ESPWortuhr/Multilayout-ESP-Wordclock/pics/CNC_Machined/uhr242_beschriftung.jpg

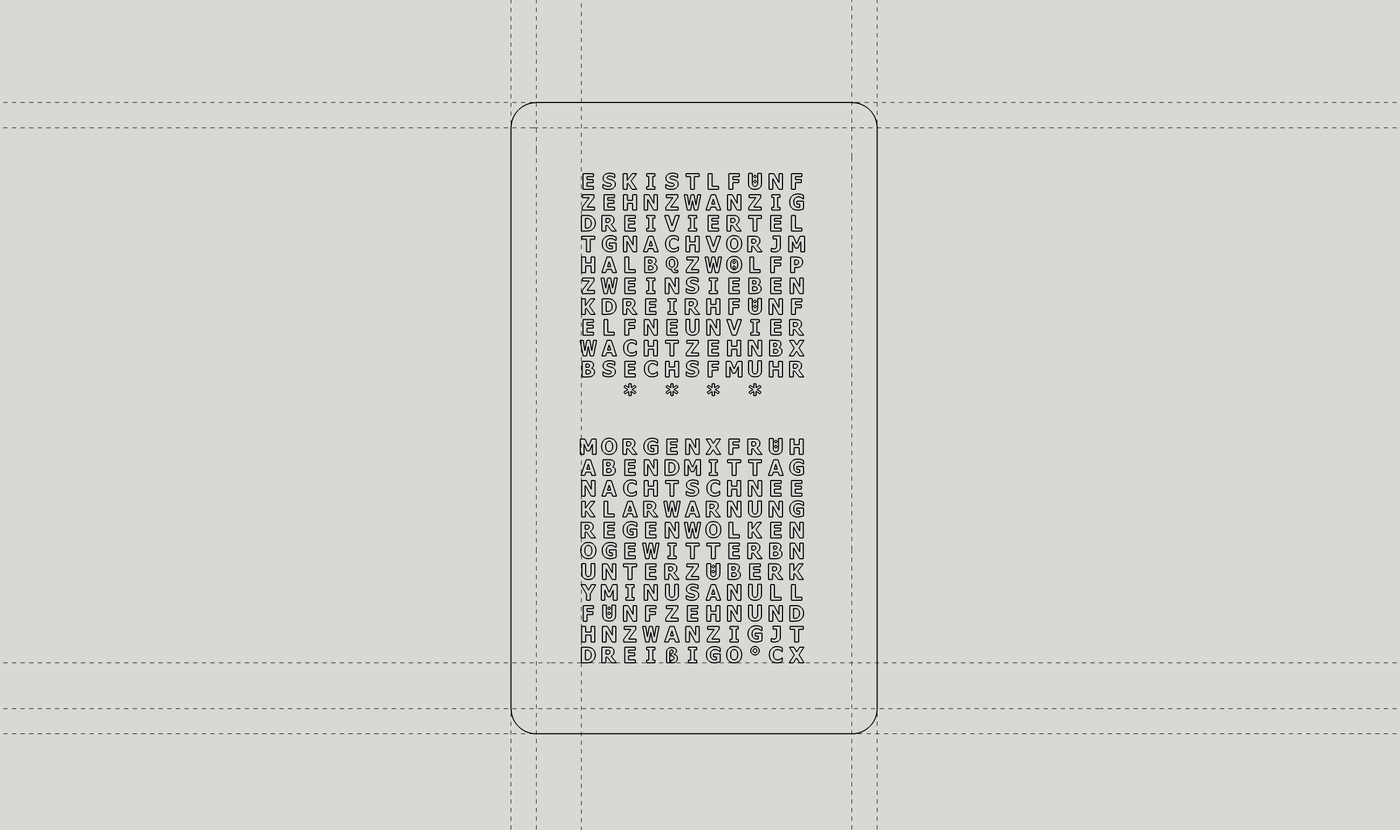
pics/CNC_Machined/uhr242_beschriftung.jpg
