ESPWortuhr/Multilayout-ESP-Wordclock/pics/CNC_Machined/uhr_242-back.jpg

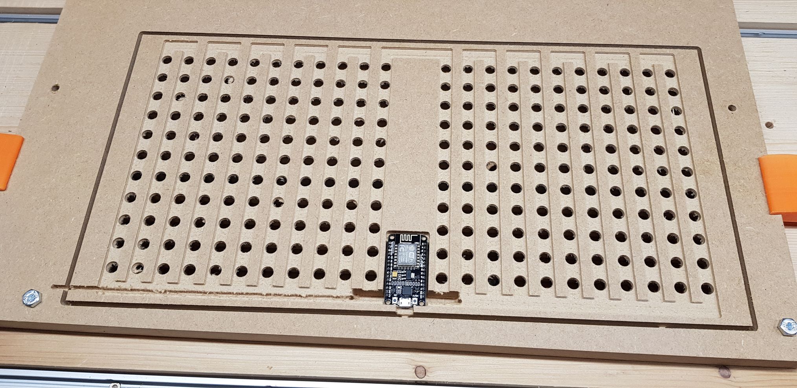
pics/CNC_Machined/uhr_242-back.jpg
