ESPWortuhr/Multilayout-ESP-Wordclock/pics/uhr.jpg

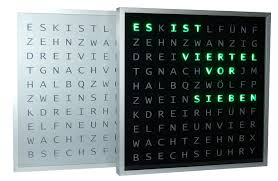
pics/uhr.jpg
