ESPWortuhr/Multilayout-ESP-Wordclock/pics/Lasercutted/UHR114_Step_1.jpg

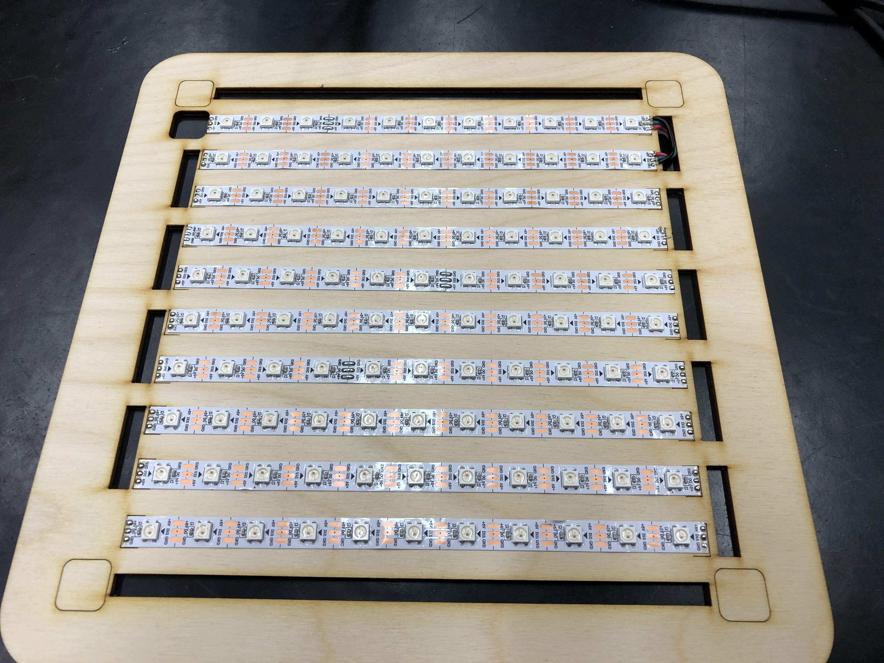
pics/Lasercutted/UHR114_Step_1.jpg
