ESPWortuhr/Multilayout-ESP-Wordclock/pics/Lasercutted/UHR114_Step_2.jpg

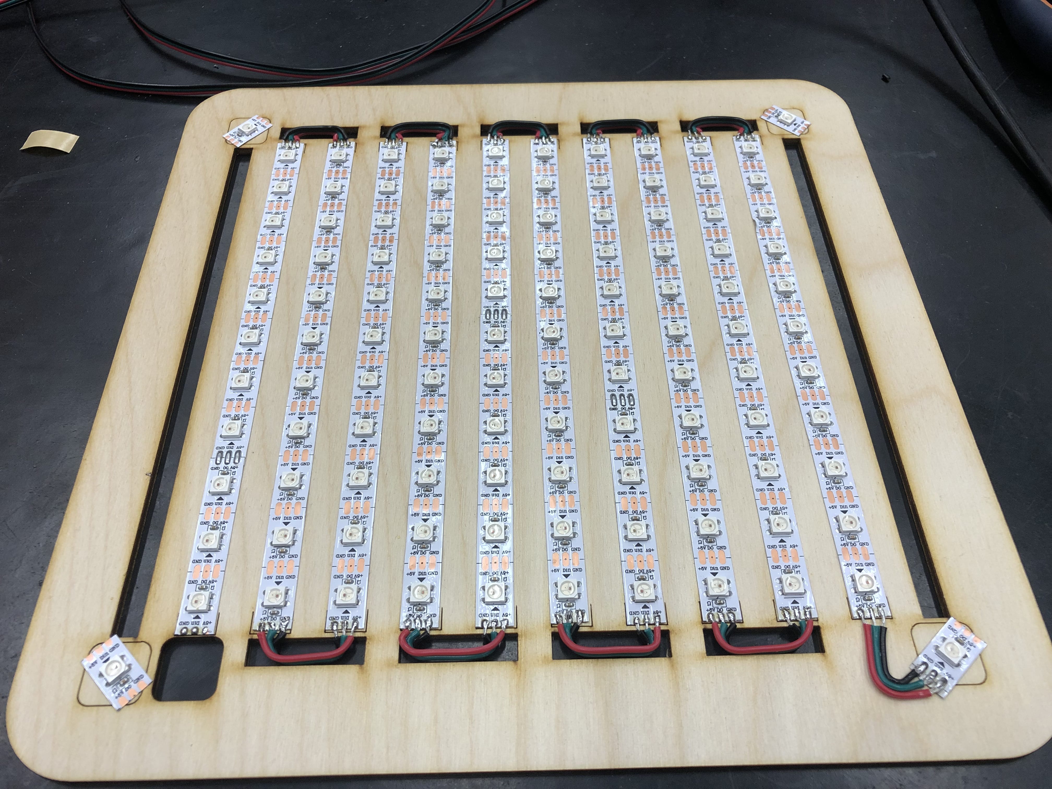
pics/Lasercutted/UHR114_Step_2.jpg
