ESPWortuhr/Multilayout-ESP-Wordclock/pics/Lasercutted/UHR114_Step_3.jpg

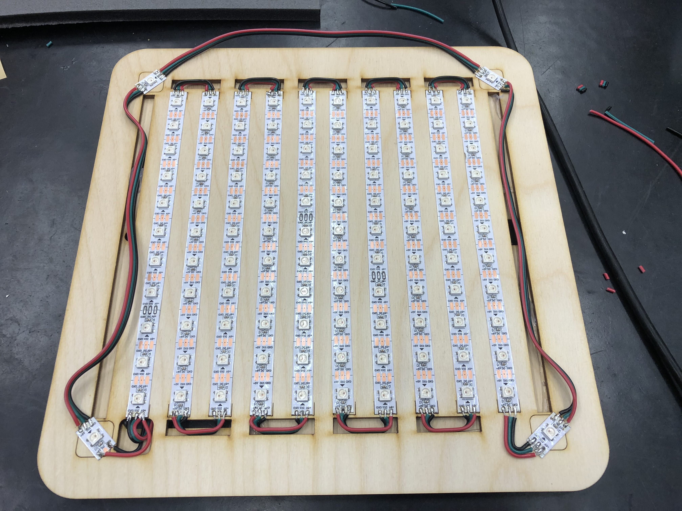
pics/Lasercutted/UHR114_Step_3.jpg
