ESPWortuhr/Multilayout-ESP-Wordclock/pics/Lasercutted/UHR114_Step_Front_Assembly.jpg

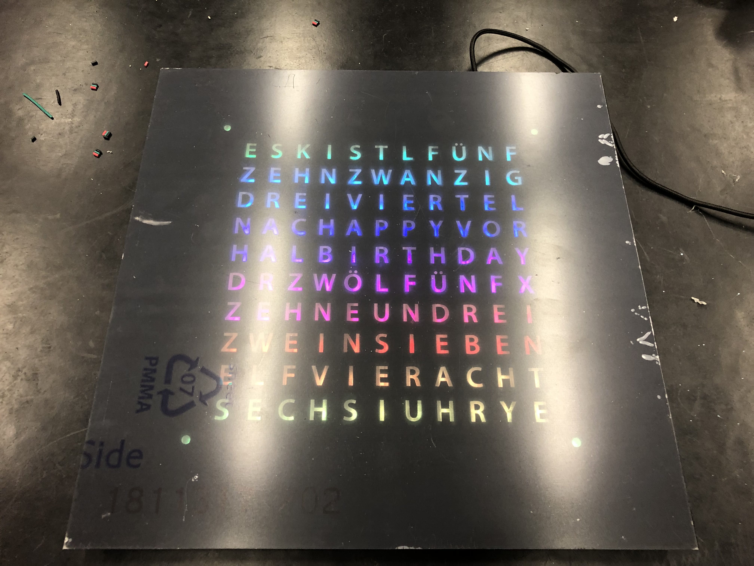
pics/Lasercutted/UHR114_Step_Front_Assembly.jpg
