ESPWortuhr/Multilayout-ESP-Wordclock/src/Wortuhr.ino

/*
 * Standard Wortuhr Konfiguration. Kann später in den Einstellungen auf der
 * Webseite geändert werden.
 */

// Layout der Frontplatte:
// - Uhr_114
//   10 Reihen, jeweils 11 LED's pro Reihe + 4 LED's für Minuten
// - Uhr_114_Alternative
//   10 Reihen, jeweils 11 LED's pro Reihe + 4 LED's für Minuten, mit geändertem
//   Layout für extra Wörter in der Matrix
// - Uhr_114_2Clock
//   10 Reihen, jeweils 11 LED's pro Reihe + 4 LED's für Minuten, mit dem Layout
//   vom orginal Hersteller
// - Uhr_125
//   11 Reihen, jeweils 11 LED's pro Reihe + 4 LED's für Minuten
// - Uhr_169
//   mit zusätzlichen LED's um den Rahmen seitlich zu beleuchten
// - Uhr_242
//   Uhr mit Wettervorhersage 242 LED's
// - Uhr_291
//   Uhr mit 24 Stunden Anzeige 18x16
#define DEFAULT_LAYOUT Uhr_114

// Typ der LEDs:
// - Brg, Grb, Rgb, Rbg (WS2812b)
// - Grbw (SK6812)
#define DEFAULT_LEDTYPE Brg

// External Realtime Clock: RTC_DS1307, RTC_PCF8523 oder RTC_DS3231
#define RTC_Type RTC_DS3231

// um das eeprom zu löschen, bzw. zu initialisieren, hier eine andere
// Seriennummer eintragen!
#define SERNR 100

bool DEBUG = true; // DEBUG ON|OFF wenn auskommentiert
//#define VERBOSE          // DEBUG VERBOSE Openweathermap

/*--------------------------------------------------------------------------
 * ENDE Hardware Konfiguration. Ab hier nichts mehr aendern!!!
 *--------------------------------------------------------------------------
 */

#include <Arduino.h>
#include <ArduinoJson.h>
#include <ESP8266HTTPUpdateServer.h>
#include <ESP8266WebServer.h>
#include <ESP8266WiFi.h>
#include <ESP8266mDNS.h>
#include <Hash.h>
#include <NeoPixelBus.h>
#include <PubSubClient.h>
#include <RTClib.h>
#include <WiFiClient.h>
#include <WiFiUdp.h>
#include <Wire.h>
#include <coredecls.h>
#include <sntp.h>

#include "Uhr.h"

#include "EEPROMAnything.h"
#include "WebPage_Adapter.h"

#include "Uhrtypes/uhr_func_114.hpp"
#include "Uhrtypes/uhr_func_114_2Clock.hpp"
#include "Uhrtypes/uhr_func_114_Alternative.hpp"
#include "Uhrtypes/uhr_func_125.hpp"
#include "Uhrtypes/uhr_func_125_Type2.hpp"
#include "Uhrtypes/uhr_func_169.hpp"
#include "Uhrtypes/uhr_func_242.hpp"
#include "Uhrtypes/uhr_func_291.hpp"

UHR_114_t Uhr_114_type;
UHR_114_Alternative_t Uhr_114_Alternative_type;
UHR_114_2Clock_t Uhr_114_2Clock_type;
UHR_125_t Uhr_125_type;
UHR_125_Type2_t Uhr_125_type2_type;
UHR_169_t Uhr_169_type;
UHR_242_t Uhr_242_type;
UHR_291_t Uhr_291_type;

iUhrType *usedUhrType = nullptr;

#include "NeoMultiFeature.hpp"
NeoPixelBus<NeoMultiFeature, Neo800KbpsMethod> *strip_RGB = NULL;
NeoPixelBus<NeoGrbwFeature, Neo800KbpsMethod> *strip_RGBW = NULL;

WiFiClient client;
PubSubClient mqttClient(client);

//--OTA--
ESP8266WebServer httpServer(81);
ESP8266HTTPUpdateServer httpUpdater;
//--OTA--

// Timezone from
// https://github.com/nayarsystems/posix_tz_db/blob/master/zones.csv
const char TZ_Europe_Berlin[] = "CET-1CEST,M3.5.0,M10.5.0/3";

RTC_Type RTC;

#include "Animation.h"
#include "font.h"
#include "icons.h"
#include "mqtt_func.hpp"
#include "openwmap.h"
#include "uhr_func.hpp"
#include "wifi_func.hpp"

#include "Animation.hpp"

Animation *animation;

#define EEPROM_SIZE 512
_Static_assert(sizeof(G) <= EEPROM_SIZE,
               "Datenstruktur G zu gross für reservierten EEPROM Bereich");
//------------------------------------------------------------------------------

iUhrType *getPointer(uint8_t num) {
    switch (num) {
    case 1:
        return reinterpret_cast<iUhrType *>(&Uhr_114_type);
    case 2:
        return reinterpret_cast<iUhrType *>(&Uhr_114_Alternative_type);
    case 6:
        return reinterpret_cast<iUhrType *>(&Uhr_114_2Clock_type);
    case 3:
        return reinterpret_cast<iUhrType *>(&Uhr_125_type);
    case 8:
        return reinterpret_cast<iUhrType *>(&Uhr_125_type2_type);
    case 4:
        return reinterpret_cast<iUhrType *>(&Uhr_169_type);
    case 5:
        return reinterpret_cast<iUhrType *>(&Uhr_242_type);
    case 7:
        return reinterpret_cast<iUhrType *>(&Uhr_291_type);
    default:
        return nullptr;
    }
}

//------------------------------------------------------------------------------

void InitLedStrip(uint8_t num) {
    NeoMultiFeature::setColortype(num);
    if (num == Grbw) {
        if (strip_RGB != NULL) {
            delete strip_RGB; // delete the previous dynamically created strip
            strip_RGB = NULL;
        }
        if (strip_RGBW == NULL) {
            strip_RGBW = new NeoPixelBus<NeoGrbwFeature, Neo800KbpsMethod>(
                usedUhrType->NUM_PIXELS());
            strip_RGBW->Begin();
        }
    } else {
        if (strip_RGBW != NULL) {
            delete strip_RGBW; // delete the previous dynamically created strip
            strip_RGBW = NULL;
        }
        if (strip_RGB == NULL) {
            strip_RGB = new NeoPixelBus<NeoMultiFeature, Neo800KbpsMethod>(
                usedUhrType->NUM_PIXELS());
            strip_RGB->Begin();
        }
    }
}

uint32_t sntp_startup_delay_MS_rfc_not_less_than_60000() {
    if (externalRTC) {
        Serial.println("SNTP startup delay 1min");
        return 60000;
    } else {
        // yes this is against the RFC, but we don't have an RTC and want the
        // time now.
        Serial.println("no RTC clock - disable SNTP startup delay");
        return 500;
    }
}

void time_is_set() {
    time_t utc = time(nullptr);
    if (externalRTC) {
        RTC.adjust(DateTime(utc));
    }

    struct tm tm;
    localtime_r(&utc, &tm);
    _sekunde = tm.tm_sec;
    _minute = tm.tm_min;
    _stunde = tm.tm_hour;
    if (usedUhrType->hasSecondsFrame()) {
        _sekunde48 = _sekunde * 48 / 60;
    }

    String origin;
    if (sntp_getreachability(0)) {
        origin = sntp_getservername(0);
        if (origin.length() == 0) {
            origin = IPAddress(sntp_getserver(0)).toString();
        }
    } else {
        origin = "SNTP not reachable";
    }
    Serial.printf("Set new time: %02d:%02d:%02d (%s)\n", _stunde, _minute,
                  _sekunde, origin.c_str());
}

//------------------------------------------------------------------------------
// Start setup()
//------------------------------------------------------------------------------

void setup() {
    //-------------------------------------
    // Start Serielle Schnittstelle bei Bedarf
    //-------------------------------------
    if (DEBUG == true) {
        Serial.begin(115200);
        Serial.println("");
        Serial.println("--------------------------------------");
        Serial.println("Begin Setup");
        Serial.println("--------------------------------------");
    }
    //-------------------------------------
    // EEPROM lesen / initialisieren
    //-------------------------------------
    EEPROM.begin(EEPROM_SIZE);

    eeprom_read();

    if (G.sernr != SERNR) {
        for (uint16_t i = 0; i < EEPROM_SIZE; i++) {
            EEPROM.write(i, i);
        }
        EEPROM.commit();

        G.sernr = SERNR;
        G.prog = 1;
        G.param1 = 0;
        G.prog_init = 1;
        G.conf = COMMAND_IDLE;
        for (uint8_t i = 0; i < 4; i++) {
            for (uint8_t ii = 0; ii < 4; ii++) {
                G.rgb[i][ii] = 0;
            }
        }
        G.rgb[Foreground][2] = 100;
        G.rgb[Effect][1] = 100;
        G.rr = 0;
        G.gg = 0;
        G.bb = 0;
        G.ww = 0;
        G.hell = 2;
        G.geschw = 10;
        G.client_nr = 0;
        G.zeige_sek = 0;
        G.zeige_min = 1;
        G.ldr = 0;
        G.ldrCal = 0;
        strcpy(G.cityid, "");
        strcpy(G.apikey, "");
        strcpy(G.zeitserver, "europe.pool.ntp.org");
        strcpy(G.hostname, "uhr");
        strcpy(G.ltext, "HELLO WORLD ");

        G.hh = 100;
        G.h6 = 100;
        G.h8 = 100;
        G.h12 = 100;
        G.h16 = 100;
        G.h18 = 100;
        G.h20 = 100;
        G.h22 = 100;
        G.h24 = 100;
        for (uint8_t i = 0; i < 5; i++) {
            G.Sprachvariation[i] = false;
        }

        G.MQTT_State = 0;
        G.MQTT_Port = 1883;
        strcpy(G.MQTT_Server, "192.168.4.1");
        strcpy(G.MQTT_User, "User");
        strcpy(G.MQTT_Pass, "Passwort");
        strcpy(G.MQTT_ClientId, "ClientId");
        strcpy(G.MQTT_Topic, "Wortuhr");

        G.UhrtypeDef = DEFAULT_LAYOUT;
        G.Colortype = DEFAULT_LEDTYPE;
        G.bootLedBlink = false;
        G.bootLedSweep = false;
        G.bootShowWifi = true;
        G.bootShowIP = false;

        G.autoLdrEnabled = 0;
        G.autoLdrBright = 100;
        G.autoLdrDark = 10;
        G.animType = 0; // Animation::KEINE;
        G.animDuration = 2;
        G.animSpeed = 30;
        G.animColorize = 1;
        G.animDemo = false;

        eeprom_write();
        Serial.println("eeprom schreiben");
    }
    // Initialisierung der COMMAND_MODE_xxx (Farbe)
    G.prog_init = 1;

    //-------------------------------------
    // Get Pointer for Uhrtype
    //-------------------------------------

    usedUhrType = getPointer(G.UhrtypeDef);

    // Bereich der animiert wird:
    //     LED-Rahmen horizontal
    //     LED-Rahmen vertical
    //     Anzahl Reihen (einschliesslich Rahmen)
    //     Anzahl Spalten (einschliesslich Rahmen)
    // TODO Rahmenbreite aus usedUhrTyp holen
    animation = new Animation(0, 0, usedUhrType->ROWS_MATRIX() - 1,
                              usedUhrType->COLS_MATRIX());

    //-------------------------------------
    // LEDs initialisieren
    //-------------------------------------
    Serial.println("LED Init");
    InitLedStrip(G.Colortype);
    if (G.bootLedBlink) {
        led_set_all(0x40, 0x40, 0x40, 0x40);
        led_show();
        delay(20);
    }
    if (G.bootLedSweep) {
        led_single(20);
    }
    led_clear();
    led_show();

    G.conf = COMMAND_IDLE;

    //-------------------------------------
    // Start External RealtimeClock
    //-------------------------------------

    if (RTC.begin() == true) {
        Serial.println("External RealtimeClock found");
        struct timeval tv;
        tv.tv_sec = RTC.now().unixtime();
        settimeofday(&tv, nullptr);
        Network_rtcMode();
        externalRTC = true;
    } else {
        Serial.println("No external RealtimeClock found");
        externalRTC = false;
    }
    settimeofday_cb(time_is_set);

    //-------------------------------------
    // Init Array
    //-------------------------------------

    for (uint16_t i = 0; i < usedUhrType->NUM_PIXELS(); i++) {
        Word_array_old[i] = 500;
    }

    //-------------------------------------
    // Start WiFi
    //-------------------------------------
    if (G.bootShowWifi) {
        show_icon_wlan(0);
    }
    Network_setup(G.hostname);
    int strength = Network_getQuality();
    Serial.printf("Signal strength: %i\n", strength);
    if (G.bootShowWifi) {
        show_icon_wlan(strength);
    }
    WlanStart();
    configTime(0, 0, G.zeitserver);
    setenv("TZ", TZ_Europe_Berlin, true);
    tzset();

    delay(50);
    //-------------------------------------
    // OTA--
    //-------------------------------------
    httpUpdater.setup(&httpServer);
    httpServer.onNotFound([]() {
        // redirect port 81 not found pages to port 80
        httpServer.sendHeader(
            "Location", "http://" + WiFi.localIP().toString() + "/", true);
        httpServer.send(308, "text/plain", "");
    });
    httpServer.begin();

    //-------------------------------------
    // MQTT
    //-------------------------------------

    if (G.MQTT_State == 1) {
        mqttClient.setServer(G.MQTT_Server, G.MQTT_Port);
        mqttClient.setCallback(MQTT_callback);
        mqttClient.connect(G.MQTT_ClientId, G.MQTT_User, G.MQTT_Pass);
        mqttClient.subscribe(G.MQTT_Topic);
    }

    //-------------------------------------
    // Start Websocket
    //-------------------------------------
    webSocket.begin();
    webSocket.onEvent(webSocketEvent);

    Serial.println("Websocket started");

    //-------------------------------------
    // mDNS
    //-------------------------------------
    MDNS.begin(G.hostname);
    MDNS.addService("http", "tcp", 80);
    MDNS.addService("http", "tcp", 81);

    // setup frame
    if (usedUhrType->hasSecondsFrame() && G.zeige_sek < 1 && G.zeige_min < 2) {
        set_farbe_rahmen();
    }

    //-------------------------------------
    Serial.println("--------------------------------------");
    Serial.println("ESP Uhr");
    Serial.printf("Version         : %s\n", VERSION);
    Serial.printf("Chip ID         : %08X\n", ESP.getChipId());
    Serial.printf("Flash ID        : %08X\n\n", ESP.getFlashChipId());
    Serial.printf("CPU Speed       : %u MHz \n\n", ESP.getCpuFreqMHz());

    Serial.printf("Flash real Size : %u KByte\n",
                  ESP.getFlashChipRealSize() / 1024);
    Serial.printf("Flash ide  Size : %u KByte\n",
                  ESP.getFlashChipSize() / 1024);
    Serial.printf("Flash ide Speed : %u\n\n", ESP.getFlashChipSpeed());

    Serial.printf("Free Heap Size  : %u Byte\n", ESP.getFreeHeap());
    Serial.printf("Sketch Size     : %u Byte \n", ESP.getSketchSize());
    Serial.printf("Free Sketch Size: %u Byte \n\n", ESP.getFreeSketchSpace());

    Serial.printf("SDK Version     : %s\n", ESP.getSdkVersion());
    Serial.print("RESET Info      : ");
    Serial.println(ESP.getResetInfo());
    Serial.print("COMPILED        : ");
    Serial.print(__DATE__);
    Serial.print(" ");
    Serial.println(__TIME__);

    Serial.println("--------------------------------------");
    Serial.println("Ende Setup");
    Serial.println("--------------------------------------");
    Serial.println("");
}

//------------------------------------------------------------------------------
// Start loop()
//------------------------------------------------------------------------------

void loop() {
    unsigned long currentMillis = millis();
    count_delay += currentMillis - previousMillis;
    if (usedUhrType->hasSecondsFrame()) {
        count_millis48 += currentMillis - previousMillis;
    }
    previousMillis = currentMillis;

    time_t utc = time(nullptr);
    struct tm tm;
    localtime_r(&utc, &tm);
    if (utc > 100000000) {
        _sekunde = tm.tm_sec;
        _minute = tm.tm_min;
        _stunde = tm.tm_hour;
    }

    // lass die Zeit im Demo Mode der Animation schneller ablaufen
    animation->demoMode(_minute, _sekunde);

    MDNS.update();

    httpServer.handleClient();

    webSocket.loop();

    //------------------------------------------------
    // MQTT
    //------------------------------------------------
    if (G.MQTT_State == 1 && WiFi.status() == WL_CONNECTED) {
        if (!mqttClient.connected()) {
            MQTT_reconnect();
        }
        mqttClient.loop();
    }

    //------------------------------------------------
    // SecondsFrame
    //------------------------------------------------
    if (usedUhrType->hasSecondsFrame()) {
        if (count_millis48 >= interval48) {
            count_millis48 = 0;
            _sekunde48++;
            if (_sekunde48 > 47) {
                _sekunde48 = 0;
            }
        }
        if (last_sekunde48 != _sekunde48) {
            if (G.prog == 0 && G.conf == 0) {
                if (G.zeige_sek == 1 || G.zeige_min == 2) {
                    rahmen_clear();
                }
                if (G.zeige_sek > 0) {
                    show_sekunde();
                }
                led_show();
            }
            last_sekunde48 = _sekunde48;
        }
    }

    //------------------------------------------------
    // Sekunde und LDR Regelung
    //------------------------------------------------
    if (last_sekunde != _sekunde) {

        // Wetteruhr
        if (usedUhrType->hasWeatherLayout()) {
            weather_tag++;
        }

        //--- LDR Regelung
        if ((G.ldr == 1) || G.autoLdrEnabled) {
            doLDRLogic();
        }

        if (G.prog == 0 && G.conf == 0) {
            led_clear();
            G.prog = COMMAND_MODE_WORD_CLOCK;
        }
        last_sekunde = _sekunde;

        if (usedUhrType->hasWeatherLayout()) {
            if ((_sekunde == 0) | (_sekunde == 10) | (_sekunde == 20) |
                (_sekunde == 30) | (_sekunde == 40) | (_sekunde == 50)) {
                wetterswitch++;
                led_clear();
                if (wetterswitch > 4) {
                    wetterswitch = 1;
                }
                Serial.print("Wetterswitch: ");
                Serial.println(wetterswitch);
                Serial.print("WStunde: ");
                Serial.println(wstunde);
            }
        }

        char currentTime[80];
        strftime(currentTime, sizeof(currentTime), "%F %T (%z)\n", &tm);
        Serial.printf(currentTime);
    }

    animation->loop(tm); // muss periodisch aufgerufen werden

    //------------------------------------------------
    // Minute
    //------------------------------------------------
    if (last_minute != _minute) {
        _sekunde48 = 0;
        last_minute = _minute;
    }

    //------------------------------------------------
    // Wetterdaten abrufen
    //------------------------------------------------
    if (usedUhrType->hasWeatherLayout() &&
        weather_tag >= 600) { // Eisbaeeer changed for Debug (soll 600)
        weather_tag = 0;
        if (WiFi.status() == WL_CONNECTED) {
            getweather();
        }
    }

    Network_loop();

    switch (G.conf) {

    case COMMAND_RESET: // Reset
    {
        delay(500);
        ESP.reset();
        ESP.restart();
        while (true) {
        }
        break;
    }

    case COMMAND_REQUEST_MQTT_VALUES: // MQTT Config Senden
    {
        DynamicJsonDocument config(1024);
        config["command"] = "mqtt";
        config["MQTT_State"] = G.MQTT_State;
        config["MQTT_Port"] = G.MQTT_Port;
        config["MQTT_Server"] = G.MQTT_Server;
        config["MQTT_User"] = G.MQTT_User;
        config["MQTT_Pass"] = G.MQTT_Pass;
        config["MQTT_ClientId"] = G.MQTT_ClientId;
        config["MQTT_Topic"] = G.MQTT_Topic;
        serializeJson(config, str);
        Serial.print("Sending Payload:");
        Serial.println(str);
        webSocket.sendTXT(G.client_nr, str, strlen(str));
        G.conf = COMMAND_IDLE;
        break;
    }

    case COMMAND_REQUEST_CONFIG_VALUES: // Config Senden
    {
        DynamicJsonDocument config(1024);
        config["command"] = "config";
        config["ssid"] = Network_getSSID();
        config["zeitserver"] = G.zeitserver;
        config["hostname"] = G.hostname;
        config["ltext"] = G.ltext;
        config["h6"] = G.h6;
        config["h8"] = G.h8;
        config["h12"] = G.h12;
        config["h16"] = G.h16;
        config["h18"] = G.h18;
        config["h20"] = G.h20;
        config["h22"] = G.h22;
        config["h24"] = G.h24;
        for (uint8_t i = 0; i < 5; i++) {
            sprintf(s, "spv%d", i);
            config[s] = G.Sprachvariation[i];
        }
        config["hell"] = G.hell;
        config["zeige_sek"] = G.zeige_sek;
        config["zeige_min"] = G.zeige_min;
        config["ldr"] = G.ldr;
        config["ldrCal"] = G.ldrCal;
        config["cityid"] = G.cityid;
        config["apikey"] = G.apikey;
        config["colortype"] = G.Colortype;
        config["UhrtypeDef"] = G.UhrtypeDef;
        config["bootLedBlink"] = G.bootLedBlink;
        config["bootLedSweep"] = G.bootLedSweep;
        config["bootShowWifi"] = G.bootShowWifi;
        config["bootShowIP"] = G.bootShowIP;
        config["hasDreiviertel"] = usedUhrType->hasDreiviertel();
        config["hasZwanzig"] = usedUhrType->hasZwanzig();
        config["hasWeatherLayout"] = usedUhrType->hasWeatherLayout();
        config["hasSecondsFrame"] = usedUhrType->hasSecondsFrame();
        serializeJson(config, str);
        Serial.print("Sending Payload:");
        Serial.println(str);
        webSocket.sendTXT(G.client_nr, str, strlen(str));
        G.conf = COMMAND_IDLE;
        break;
    }

    case COMMAND_REQUEST_COLOR_VALUES: // Config Farbwerte senden
    {
        DynamicJsonDocument config(1024);
        config["command"] = "set";
        for (uint8_t i = 0; i < 4; i++) {
            for (uint8_t ii = 0; ii < 4; ii++) {
                sprintf(s, "rgb%d%d", i, ii);
                config[s] = G.rgb[i][ii];
            }
        }
        config["hell"] = G.hell;
        config["geschw"] = G.geschw;
        config["colortype"] = G.Colortype;
        config["prog"] = G.prog;
        serializeJson(config, str);
        webSocket.sendTXT(G.client_nr, str, strlen(str));
        G.conf = COMMAND_IDLE;
        break;
    }

    case COMMAND_REQUEST_AUTO_LDR: // Automatische Helligkeit
    {
        DynamicJsonDocument config(1024);
        config["command"] = "autoLdr";
        if (G.param1 == 0) {
            config["autoLdrEnabled"] = G.autoLdrEnabled;
            config["autoLdrBright"] = G.autoLdrBright;
            config["autoLdrDark"] = G.autoLdrDark;
        }
        config["autoLdrValue"] = map(analogRead(A0), 0, 1023, 0, 255);
        serializeJson(config, str);
        webSocket.sendTXT(G.client_nr, str, strlen(str));
        G.conf = COMMAND_IDLE;
        break;
    }

    case COMMAND_REQUEST_ANIMATION: // Animation
    {
        DynamicJsonDocument config(1024);
        config["command"] = "animation";
        config["animType"] = G.animType;
        config["animDuration"] = G.animDuration;
        config["animSpeed"] = G.animSpeed;
        config["animDemo"] = G.animDemo;
        config["animColorize"] = G.animColorize;
        JsonArray types = config.createNestedArray("animTypes");
        // Reihenfolge muss zu enum Ani passen!
        types.add("keine");
        types.add("Hoch rollen");
        types.add("Runter rollen");
        types.add("Links schieben");
        types.add("Rechts schieben");
        types.add("Überblenden");
        types.add("Laser");
        types.add("Matrix");
        types.add("Baelle");
        types.add("Feuerwerk");
        types.add("Schlange");
        types.add("zufällig");
        serializeJson(config, str);
        webSocket.sendTXT(G.client_nr, str, strlen(str));
        G.conf = COMMAND_IDLE;
        break;
    }

    case COMMAND_SET_TIME:           // Uhrzeit setzen
    case COMMAND_SET_INITIAL_VALUES: // Startwerte speichern
    case COMMAND_SET_BRIGHTNESS:     // Helligkeit speichern
    case COMMAND_SET_MINUTE:         // Anzeige Minuten speichern
    case COMMAND_SET_LDR:            // LDR Einstellung speichern
    case COMMAND_SET_AUTO_LDR:       // Auto LDR Parameter speichern
    case COMMAND_SET_WEATHER_DATA:   // OpenWeathermap Einstellung speichern
    case COMMAND_SET_MARQUEE_TEXT:   // Lauftext speichern
    case COMMAND_SET_BOOT:           // Bootoptionen speichern
    {
        eeprom_write();
        delay(100);
        G.conf = COMMAND_IDLE;
        break;
    }

    case COMMAND_SET_LANGUAGE_VARIANT: // Sprachvarianten Einstellungen
    case COMMAND_SET_SETTING_SECOND:   // Anzeige Sekunde speichern
    case COMMAND_SET_TIME_MANUAL:      // Uhrzeit manuell einstellen
    {
        eeprom_write();
        led_clear();
        G.prog = COMMAND_MODE_WORD_CLOCK;
        G.conf = COMMAND_IDLE;
        break;
    }

    case COMMAND_SET_MQTT: // MQTT Einstellungen
    {
        if (!mqttClient.connected() && G.MQTT_State) {
            mqttClient.connect(G.MQTT_ClientId, G.MQTT_User, G.MQTT_Pass);
            MQTT_reconnect();
        }
        eeprom_write();
        G.conf = COMMAND_IDLE;
        break;
    }

    case COMMAND_SET_COLORTYPE: // Colortype der LED einstellen
    {
        // G.param1 enthält den neuen Colortype
        Serial.printf("LED Colortype: %u\n", G.param1);

        // if ((G.param1 != G.Colortype) && ((G.param1 == Grbw) ||
        //    (G.Colortype == Grbw))) {
        //    G.conf = COMMAND_RESET;
        // } else {
        G.conf = COMMAND_IDLE;
        // }

        // der G.Colortype muss zeitgleich zu InitLedStrip erfolgen,
        // sonst wird über einen null-pointer referenziert
        G.Colortype = G.param1;
        eeprom_write();
        InitLedStrip(G.Colortype);
        led_set_Icon(RGB_I, 100, true);
        break;
    }

    case COMMAND_SET_UHRTYPE: // Uhrtype Layout einstellen
    {
        eeprom_write();
        Serial.printf("Uhrtype: %u\n", G.UhrtypeDef);
        usedUhrType = getPointer(G.UhrtypeDef);
        G.conf = COMMAND_IDLE;
        break;
    }

    case COMMAND_SET_HOSTNAME: // Hostname speichern
    {
        Serial.print("Hostname: ");
        Serial.println(G.hostname);
        eeprom_write();
        Network_reboot();
        G.conf = COMMAND_IDLE;
        break;
    }

    case COMMAND_SET_WIFI_DISABLED: // WLAN-Daten speichern und neu starten
    {
        eeprom_write();
        delay(100);
        Serial.println("Conf: WLAN Abgeschaltet");
        Network_disable();
        G.conf = COMMAND_IDLE;
        break;
    }

    case COMMAND_SET_WIFI_AND_RESTART: // WLAN-Daten speichern und neu starten
    {
        Serial.println("Conf: WLAN neu konfiguriert");
        Network_resetSettings();
        G.conf = COMMAND_IDLE;
        break;
    }

    default:
        break;
    }

    switch (G.prog) {

    case COMMAND_MODE_SECONDS: // Sekundenanzeige
    {
        if (G.prog_init == 1) {
            led_clear();
            G.prog_init = 0;
        }
        char d1[5];
        char d2[5];
        sprintf(d1, "%d", (int)(_sekunde / 10));
        sprintf(d2, "%d", (int)(_sekunde % 10));
        zahlen(d1[0], d2[0]);
        break;
    }

    case COMMAND_MODE_MARQUEE: // Laufschriftanzeige
    {
        if (G.prog_init == 1) {
            G.prog_init = 0;
            led_clear();
            count_delay = (G.geschw + 1) * 20;
        }
        if (count_delay >= (G.geschw + 1u) * 20u) {
            laufschrift(G.ltext);
            count_delay = 0;
        }
        break;
    }

    case COMMAND_MODE_RAINBOW: // Regenbogenanzeige
    {
        if (G.prog_init == 1) {
            G.prog_init = 0;
            uhr_clear();
            count_delay = G.geschw * 7 + 1;
        }
        if (count_delay >= G.geschw * 7u + 1u) {
            rainbowCycle();
            count_delay = 0;
        }
        break;
    }

    case COMMAND_MODE_CHANGE: // Farbwechselanzeige
    {
        if (G.prog_init == 1) {
            G.prog_init = 0;
            led_clear();
            count_delay = G.geschw * 7 + 1;
        }
        if (count_delay >= G.geschw * 7u + 1u) {
            rainbow();
            count_delay = 0;
        }
        break;
    }

    case COMMAND_MODE_COLOR: // Farbe Rahmen
    {
        if (G.prog_init == 1) {
            G.prog_init = 0;
            set_farbe();
            led_show();
        }
        break;
    }

    case COMMAND_MODE_ANIMATION: // Animation
    {
        if (G.prog_init == 1) {
            G.prog_init = 0;
            eeprom_write();
            delay(100);
        }
        // Hier ist mit Absicht kein break, direkt nach dem Call
        // COMMAND_MODE_ANIMATION muss COMMAND_MODE_WORD_CLOCK aufgerufen
        // werden.
    }

    case COMMAND_MODE_WORD_CLOCK: {
        calc_word_array();

        if (changes_in_array()) {
            copy_array(Word_array, Word_array_old);
            led_set(true);
        } else if (parameters_changed) {
            led_set();
        }
        parameters_changed = false;

        if (usedUhrType->hasSecondsFrame() && G.zeige_sek < 1 &&
            G.zeige_min < 2) {
            set_farbe_rahmen();
        }
        G.prog = COMMAND_IDLE;
    }
    default:
        break;
    }

    if (count_delay > 10000) {
        count_delay = 0;
    }
}
