ESPWortuhr/Multilayout-ESP-Wordclock/include/ClockWork.hpp

#include "ClockWork.h"
#include "I2CBus.h"
#include "NeoMultiFeature.hpp"
#include "OpenWeatherMap.h"
#include "SensitiveData.h"
#include "TransitionTypes/Transition.h"
#include "WordClockState.h"
#include "WordClockTypes/ClockType.hpp"
#include "math.h"
#include <Arduino.h>
#include <BH1750.h>

#define MAX_LED_COUNT 300

BH1750 lightMeter;
OpenWMap weather;

uint8_t activeLedPin = UINT8_MAX;
uint8_t activeLedColorType = UINT8_MAX;
uint16_t activeLedCount = 0;

//------------------------------------------------------------------------------
// Helper Functions
//------------------------------------------------------------------------------

/*
Automatic Brightness Control (enabled/disabled by G.autoBrightEnabled)

1. Measure ambient light with sensor BH1750, if available. If not, use LDR.
2. Derive the ledGain for the LEDs 0.0 - 100.0%
3. When ledGain changed, set parametersChanged = true

Inputs:
G.autoBrightEnabled, G.autoBrightMin, G.autoBrightMax, G.autoBrightPeak
AUTOBRIGHT_LDR_RESBRIGHT, AUTOBRIGHT_LDR_RESDARK, AUTOBRIGHT_LDR_RESDIVIDER

Outputs:
lux = Ambient light [LUX]
ledGain = gain for LEDs: 0.0-100.0% (n % of the configured bri:effectBri)
*/

void ClockWork::loopAutoBrightLogic() {
    if (G.autoBrightEnabled != 1)
        return;

    if (G.autoBrightMin == G.autoBrightMax) {
        // If min and max are identical, nothing needs to be measured...
        // Besides: map() would crash with division by zero in this case
        ledGain = G.autoBrightMax;
        return;
    }

    float ledGainOld = ledGain;
    float luxNow = -1.0;

    if (bh1750Initialized && lightMeter.measurementReady()) {
        /*
        If BH1750 is not available or did not return a value, try to use LDR
        */
        luxNow = lightMeter.readLightLevel(); // 0.0-54612.5 LUX
        autoBrightUsingBH1750 = true;
    }

    else if (luxNow < 0) {
        /*
        The lux value is considerably misrepresented upwards at ADC values above
        980. As 980 with an LDR5528 corresponds to approx. 1500 lux, but usually
        no more than 1000 lux are reached indoors even on sunny days, a fixed
        upper measurement limit of 980 is set here. Regardless of this, a
        maximum value of 1023 has to be applied in any case in order to avoid
        division by zero (analogRead is 0-1023)!
        */
        uint16_t adcValue = analogRead(A0);
        if (adcValue > 980) {
            adcValue = 980;
        }

        luxNow = (adcValue * AUTOBRIGHT_LDR_RESDARK * 10) /
                 (AUTOBRIGHT_LDR_RESBRIGHT * AUTOBRIGHT_LDR_RESDIVIDER *
                  (1024 - adcValue));
        autoBrightUsingBH1750 = false;
    }

    else {
        /*
        If luxNow is still negative, no data could be retrieved from BH1750 or
        LDR. We return to preserve the previous ledGain (potentially default).
        Otherwise we may end up in a blinking light.
        */
        return;
    }

    /*
    Even in HIGH_RES_MODE, the BH1750 only has a precision of 1 lux. The decimal
    point values supplied by the library should therefore be considered as
    'noise' and their use makes little to no sense. Also: in order to not
    trigger parametersChanged more often than necessary, the value gets rounded.
    */

    lux = round(luxNow);

    ledGain = map(lux, 0, G.autoBrightPeak, G.autoBrightMin, G.autoBrightMax);

    // Ensure ledGain meets the defined limits.
    uint16_t minimum = min(G.autoBrightMin, G.autoBrightMax);
    uint16_t maximum = max(G.autoBrightMin, G.autoBrightMax);

    if (ledGain >= maximum) {
        ledGain = maximum;
    }
    if (ledGain <= minimum) {
        ledGain = minimum;
    }

    if (ledGainOld != ledGain) {
        parametersChanged = true;
    }
}

//------------------------------------------------------------------------------

void ClockWork::initHardwareButtons() {
    hardwareButtonController.begin(G.hardwarePins);
}

//------------------------------------------------------------------------------

void ClockWork::toggleHardwareButtonPower() {
    led.setState(!led.getState());

    requestHardwareButtonDisplayRefresh();
}

//------------------------------------------------------------------------------

void ClockWork::nextHardwareButtonMode() {
    static const uint8_t modes[] = {
        COMMAND_MODE_WORD_CLOCK,    COMMAND_MODE_SECONDS,
        COMMAND_MODE_SCROLLINGTEXT, COMMAND_MODE_RAINBOWCYCLE,
        COMMAND_MODE_RAINBOW,       COMMAND_MODE_COLOR,
        COMMAND_MODE_DIGITAL_CLOCK, COMMAND_MODE_SYMBOL};

    uint8_t nextMode = modes[0];
    for (uint8_t i = 0; i < sizeof(modes) / sizeof(modes[0]); i++) {
        if (G.prog == modes[i] ||
            (G.prog == COMMAND_IDLE && modes[i] == COMMAND_MODE_WORD_CLOCK)) {
            nextMode = modes[(i + 1) % (sizeof(modes) / sizeof(modes[0]))];
            break;
        }
    }

    G.prog = nextMode;
    G.progInit = true;
    parametersChanged = true;
}

//------------------------------------------------------------------------------

void ClockWork::nextHardwareButtonTransition() {
    static const uint8_t transitions[] = {
        NO_TRANSITION, ROLL_UP, ROLL_DOWN,   SHIFT_LEFT, SHIFT_RIGHT,
        FADE,          LASER,   MATRIX_RAIN, BALLS,      FIRE,
        SNAKE,         COLORED, RANDOM};

    uint8_t nextTransition = transitions[0];
    for (uint8_t i = 0; i < sizeof(transitions) / sizeof(transitions[0]); i++) {
        if (G.transitionType == transitions[i]) {
            nextTransition = transitions[(i + 1) % (sizeof(transitions) /
                                                    sizeof(transitions[0]))];
            break;
        }
    }

    G.transitionType = nextTransition;
    G.prog = COMMAND_MODE_TRANSITION;
    G.progInit = true;
    parametersChanged = true;
}

//------------------------------------------------------------------------------

void ClockWork::increaseHardwareButtonBrightness() {
    float brightness = G.color[Foreground].B;
    if (brightness <= 0.0f) {
        brightness = 0.1f;
    } else if (brightness >= 1.0f) {
        brightness = 0.1f;
    } else {
        brightness += 0.1f;
        if (brightness > 1.0f) {
            brightness = 1.0f;
        }
    }

    G.color[Foreground].B = brightness;
    requestHardwareButtonDisplayRefresh();
}

//------------------------------------------------------------------------------

void ClockWork::nextHardwareButtonHue() {
    float hue = G.color[Foreground].H + (30.0f / 360.0f);
    if (hue >= 1.0f) {
        hue -= 1.0f;
    }
    G.color[Foreground].H = hue;
    requestHardwareButtonDisplayRefresh();
}

//------------------------------------------------------------------------------

void ClockWork::requestHardwareButtonDisplayRefresh() {
    parametersChanged = true;
    if (G.prog == COMMAND_IDLE) {
        G.prog = COMMAND_MODE_WORD_CLOCK;
    }
}

//------------------------------------------------------------------------------

void ClockWork::handleHardwareButtonAction(HardwareButtonAction action) {
    switch (action) {
    case HardwareButtonAction::TogglePower:
        toggleHardwareButtonPower();
        break;
    case HardwareButtonAction::NextMode:
        nextHardwareButtonMode();
        break;
    case HardwareButtonAction::NextTransition:
        nextHardwareButtonTransition();
        break;
    case HardwareButtonAction::IncreaseBrightness:
        increaseHardwareButtonBrightness();
        break;
    case HardwareButtonAction::NextHue:
        nextHardwareButtonHue();
        break;
    default:
        break;
    }
}

//------------------------------------------------------------------------------

void ClockWork::loopHardwareButtons() {
    const HardwareButtonAction action = hardwareButtonController.loop();
    if (action != HardwareButtonAction::None) {
        handleHardwareButtonAction(action);
    }
}

//------------------------------------------------------------------------------

ClockType *ClockWork::getPointer(uint8_t type) {
    switch (type) {
#define X(name, id, var, i18n)                                                 \
    case name:                                                                 \
        return &var;
        CLOCK_TYPES_LIST
#undef X
    default:
        return nullptr;
    }
}

//------------------------------------------------------------------------------

void ClockWork::initLedStrip(uint8_t num) {
    NeoMultiFeature::setColortype(num);
    const uint16_t ledCount = MAX_LED_COUNT * getLedsPerLetter(G.buildTypeDef);

    if (activeLedPin != G.hardwarePins.led || activeLedColorType != num ||
        activeLedCount != ledCount) {
        deleteActiveLedStrip();
        activeLedPin = G.hardwarePins.led;
        activeLedColorType = num;
        activeLedCount = ledCount;
    }

    if (activeLedStrip != nullptr) {
        return;
    }

#ifdef ESP8266
    if (num == Grbw) {
        if (G.hardwarePins.led == LED_PIN) {
            activeLedStrip =
                new RgbwLedStripAdapter<Neo800KbpsMethod>(ledCount);
        } else {
            activeLedStrip =
                new RgbwLedStripAdapter<NeoEsp8266BitBangWs2812xMethod>(
                    ledCount, G.hardwarePins.led);
        }
    } else if (G.hardwarePins.led == LED_PIN) {
        activeLedStrip = new RgbLedStripAdapter<Neo800KbpsMethod>(ledCount);
    } else {
        activeLedStrip = new RgbLedStripAdapter<NeoEsp8266BitBangWs2812xMethod>(
            ledCount, G.hardwarePins.led);
    }
#else
#if defined(ESP32)
    pinMode(G.hardwarePins.led, OUTPUT);
#endif
    if (num == Grbw) {
        activeLedStrip = new RgbwLedStripAdapter<NeoEsp32Rmt0Ws2812xMethod>(
            ledCount, G.hardwarePins.led);
    } else {
        activeLedStrip = new RgbLedStripAdapter<NeoEsp32Rmt0Ws2812xMethod>(
            ledCount, G.hardwarePins.led);
    }
#endif
}

//------------------------------------------------------------------------------

uint32_t ClockWork::num32BitWithOnesAccordingToColumns() {
    return (1U << usedClockType->colsWordMatrix()) - 1;
}

//------------------------------------------------------------------------------

void sendJsonToClient(uint8_t client_nr, const JsonDocument &doc) {
    if (doc.overflowed()) {
        Serial.println("[ERROR] sendJsonToClient(): document capacity too "
                       "small, keys are missing");
    }

    const size_t payloadLength = measureJson(doc);

    String payload;
    payload.reserve(payloadLength + 1);
    serializeJson(doc, payload);

    if (payload.length() != payloadLength) {
        Serial.printf("[ERROR] sendJsonToClient(): out of memory for %u "
                      "bytes, payload dropped\n",
                      payloadLength + 1);
        return;
    }

    Serial.print("Sending Payload:");
    Serial.println(payload);

    webSocket.sendTXT(client_nr, payload);
}

//------------------------------------------------------------------------------

void sendI2CScanResult(uint8_t client_nr, uint8_t sdaPin, uint8_t sclPin) {
    DynamicJsonDocument config(384);
    config["command"] = "i2c-scan";
    config["sdaPin"] = sdaPin;
    config["sclPin"] = sclPin;

    JsonArray addresses = config.createNestedArray("addresses");
    i2cBus::ScanResult result =
        i2cBus::scan(sdaPin, sclPin, G.i2cSdaPin, G.i2cSclPin);

    if (result.status == i2cBus::ScanStatus::Invalid) {
        config["status"] = "invalid";
        sendJsonToClient(client_nr, config);
        return;
    }

    if (result.status == i2cBus::ScanStatus::Disabled) {
        config["status"] = "disabled";
        sendJsonToClient(client_nr, config);
        return;
    }

    for (uint8_t i = 0; i < result.addressCount; i++) {
        char addressText[5] = {0};
        snprintf(addressText, sizeof(addressText), "0x%02X",
                 result.addresses[i]);
        addresses.add(addressText);
    }

    config["status"] = "ok";
    sendJsonToClient(client_nr, config);
}

//------------------------------------------------------------------------------
// Front Effect Functions
//------------------------------------------------------------------------------

void ClockWork::rainbow() {
    static uint16_t hue = 0;

    for (uint8_t row = 0; row < usedClockType->rowsWordMatrix(); row++) {
        for (uint8_t col = 0; col < usedClockType->colsWordMatrix(); col++) {
            led.setPixel(row, col,
                         HsbColor(hue / 360.f, 1.f, G.effectBri / 100.f));
        }
    }
    led.show();
    hue++;
    led.checkIfHueIsOutOfBound(hue);
}

//-----------------------------------------------------------------------------

void ClockWork::rainbowCycle() {
    static uint16_t hue = 0;
    uint16_t numPixelsWordMatrix =
        usedClockType->rowsWordMatrix() * usedClockType->colsWordMatrix();
    uint16_t displayedHue;

    displayedHue = hue;
    for (uint8_t row = 0; row < usedClockType->rowsWordMatrix(); row++) {
        for (uint8_t col = 0; col < usedClockType->colsWordMatrix(); col++) {
            led.setPixel(
                row, col,
                HsbColor(displayedHue / 360.f, 1.f, G.effectBri / 100.f));
            displayedHue = displayedHue + 360.f / numPixelsWordMatrix;
            led.checkIfHueIsOutOfBound(displayedHue);
        }
    }
    led.show();
    hue++;
    led.checkIfHueIsOutOfBound(hue);
}

//------------------------------------------------------------------------------

void ClockWork::rainbowSpiralCycle() {
    static uint16_t hue = 0;

    uint8_t rows = usedClockType->rowsWordMatrix();
    uint8_t cols = usedClockType->colsWordMatrix();

    // 1. Calculate the center of the matrix.
    float centerRow = (rows - 1) / 2.0f;
    float centerCol = (cols - 1) / 2.0f;

    // 2. Calculate the maximum distance from the center to any corner.
    // This scales the color gradient cleanly to the matrix size.
    float maxDist = sqrt(centerRow * centerRow + centerCol * centerCol);

    for (uint8_t row = 0; row < rows; row++) {
        for (uint8_t col = 0; col < cols; col++) {

            // 3. Calculate the current pixel's distance from the center.
            float dRow = row - centerRow;
            float dCol = col - centerCol;
            float distance = sqrt(dRow * dRow + dCol * dCol);

            // 4. Calculate the color based on distance and base hue.
            // distance / maxDist returns a value between 0.0 and 1.0.
            // Multiplying it by 360 stretches the rainbow across the radius.
            float hueOffset = (distance / maxDist) * 360.0f;

            // Add the base hue, which drives the movement, and the offset.
            uint16_t pixelHue = hue + (uint16_t)hueOffset;

            // Keep generated hue values inside the 0-359 range.
            while (pixelHue >= 360) {
                pixelHue -= 360;
            }

            led.setPixel(row, col,
                         HsbColor(pixelHue / 360.f, 1.f, G.effectBri / 100.f));
        }
    }

    led.show();

    // 5. Advance the animation.
    // hue++ moves the colors inward.
    // hue-- (or hue + 359) would move the colors outward.
    hue++;
    if (hue >= 360) {
        hue = 0;
    }
}

//------------------------------------------------------------------------------

bool ClockWork::getStaticScrollingTextInfo(const char *buf,
                                           StaticScrollingText &info) {
    uint16_t textStart = 0;
    uint16_t textEnd = strlen(buf);

    auto isTrimmedWhitespace = [](char c) {
        return c == ' ' || c == '\t' || c == '\r' || c == '\n';
    };

    while (textStart < textEnd && isTrimmedWhitespace(buf[textStart])) {
        textStart++;
    }

    while (textEnd > textStart && isTrimmedWhitespace(buf[textEnd - 1])) {
        textEnd--;
    }

    uint16_t trimmedLen = textEnd - textStart;
    if (trimmedLen == 0 || trimmedLen > 2) {
        return false;
    }

    info.start = static_cast<uint8_t>(textStart);
    info.len = static_cast<uint8_t>(trimmedLen);
    info.onlyDigits = true;

    for (uint16_t i = textStart; i < textEnd; i++) {
        if (buf[i] < '0' || buf[i] > '9') {
            info.onlyDigits = false;
            break;
        }
    }

    if (!info.onlyDigits) {
        info.width = pgm_read_byte(&(fontWidth[normalSizeASCII]));
        info.height = pgm_read_byte(&(fontHeight[normalSizeASCII]));
        info.totalWidth = info.len * info.width + info.len - 1;

        if (usedClockType->colsWordMatrix() < info.totalWidth ||
            usedClockType->rowsWordMatrix() < info.height) {
            return false;
        }
    }

    return true;
}

//------------------------------------------------------------------------------

void ClockWork::displayStaticScrollingText(const char *buf,
                                           const StaticScrollingText &info) {
    if (info.onlyDigits) {
        led.showNumbers(info.len == 1 ? ' ' : buf[info.start],
                        buf[info.start + info.len - 1]);
        return;
    }

    led.clearClock();

    uint8_t offsetRow = (usedClockType->rowsWordMatrix() - info.height) / 2;
    uint8_t offsetCol = (usedClockType->colsWordMatrix() - info.totalWidth) / 2;

    for (uint8_t charIndex = 0; charIndex < info.len; charIndex++) {
        uint8_t charOffsetCol = offsetCol + charIndex * (info.width + 1);
        unsigned char fontIndex =
            static_cast<unsigned char>(buf[info.start + charIndex]);

        for (uint8_t col = 0; col < info.width; col++) {
            for (uint8_t row = 0; row < info.height; row++) {
                led.setPixelForChar(col, row, charOffsetCol, offsetRow,
                                    fontIndex, normalSizeASCII);
            }
        }
    }

    led.mirrorFrontMatrixVertical();
    led.setbyFrontMatrix(Foreground);
    led.show();
}

//------------------------------------------------------------------------------

void ClockWork::scrollingText(const char *buf) {
    static uint8_t i = 0, ii = 0;
    StaticScrollingText staticText;

    if (getStaticScrollingTextInfo(buf, staticText)) {
        i = 0;
        ii = 0;
        displayStaticScrollingText(buf, staticText);
        return;
    }

    uint8_t offsetRow = (usedClockType->rowsWordMatrix() -
                         pgm_read_byte(&(fontHeight[normalSizeASCII]))) /
                        2;

    uint16_t len = strlen(buf);
    uint8_t width = pgm_read_byte(&(fontWidth[normalSizeASCII]));
    uint8_t charsToFlush = (usedClockType->colsWordMatrix() / (width + 1)) + 1;

    if (ii >= len + charsToFlush) {
        ii = 0;
        i = 0;
    }

    uint8_t fontIndex = (ii < len) ? buf[ii] : ' ';

    led.setbyFrontMatrix(Foreground); // Needed for Mirrored Display
    led.shiftColumnToRight();
    led.clearFrontExeptofFontspace(offsetRow);

    if (i < width) {
        for (uint8_t row = 0;
             row < pgm_read_byte(&(fontHeight[normalSizeASCII])); row++) {
            usedClockType->setFrontMatrixPixel(
                row + offsetRow, 0,
                pgm_read_byte(&(font_7x5[fontIndex][i])) & (1u << row));
        }
    } else {
        for (uint8_t row = 0;
             row < pgm_read_byte(&(fontHeight[normalSizeASCII])); row++) {
            usedClockType->setFrontMatrixPixel(row + offsetRow, 0, false);
        }
    }

    led.setbyFrontMatrix(Foreground);
    led.show();

    i++;
    if (i >= width + 1) // +1 for spacing
    {
        i = 0;
        ii++;
        if (ii >= len + charsToFlush) {
            ii = 0;
        }
    }
}

//------------------------------------------------------------------------------

void ClockWork::displaySymbols(BitmapSymbol symbolNum) {
    if (symbolNum >= BitmapSymbol::MAX_BITMAP_SYMBOLS) {
        symbolNum = BitmapSymbol::HEART;
    }

    HsbColor color = G.color[Foreground];
    color.B = G.effectBri / 100.f;
    led.setBitmapSymbol(symbolNum, color);
}

//------------------------------------------------------------------------------

void ClockWork::countdownToMidnight() {
    Serial.printf("Count down: %d\n", 60 - _second);
    switch (_second) {
    case 50:
        if (!usedClockType->hasOnlyQuarterLayout()) {
            usedClockType->show(FrontWord::min_10);
        } else {
            usedClockType->show(FrontWord::hour_10);
        }
        break;
    case 51:
        usedClockType->show(FrontWord::hour_9);
        break;
    case 52:
        usedClockType->show(FrontWord::hour_8);
        break;
    case 53:
        usedClockType->show(FrontWord::hour_7);
        break;
    case 54:
        usedClockType->show(FrontWord::hour_6);
        break;
    case 55:
        if (!usedClockType->hasOnlyQuarterLayout()) {
            usedClockType->show(FrontWord::min_5);
        } else {
            usedClockType->show(FrontWord::hour_5);
        }
        break;
    case 56:
        usedClockType->show(FrontWord::hour_4);
        break;
    case 57:
        usedClockType->show(FrontWord::hour_3);
        break;
    case 58:
        usedClockType->show(FrontWord::hour_2);
        break;
    case 59:
        if (usedClockType->usedLang() == LanguageAbbreviation::DE) {
            usedClockType->show(FrontWord::eins);
        } else {
            usedClockType->show(FrontWord::hour_1);
        }
        break;
    default:
        break;
    }
}

//------------------------------------------------------------------------------
// Boot Functions
//------------------------------------------------------------------------------

void ClockWork::initBootShowIp(const char *buf) {
    uint8_t StringLength = strlen(buf);
    StringLength = StringLength * 6; // Times 6, because thats the length of a
                                     // char in the 7x5 font plus spacing
    for (uint16_t i = 0; i <= StringLength; i++) {
        scrollingText(buf);
        delay(200);
    }
}

//------------------------------------------------------------------------------

void ClockWork::initBootLedBlink() {
    for (uint8_t row = 0; row < usedClockType->rowsWordMatrix(); row++) {
        frontMatrix[row] ^= num32BitWithOnesAccordingToColumns();
    }
    led.setbyFrontMatrix(Foreground);
    led.show();
}

//------------------------------------------------------------------------------

void ClockWork::initBootLedSweep(uint32_t delay) { led.setSingle(delay); }

//------------------------------------------------------------------------------

void ClockWork::initBootLed() {
    led.clear();
    led.show();
}

//------------------------------------------------------------------------------
// Minute Functions
//------------------------------------------------------------------------------

uint8_t ClockWork::determineWhichMinuteVariant() {
    switch (G.minuteVariant) {
    case MinuteVariant::Off:
        return 0;
        break;
    case MinuteVariant::LED4x:
        return 0;
        break;
    case MinuteVariant::LED7x:
        return 1;
        break;
    case MinuteVariant::Corners:
        return 2;
        break;
    case MinuteVariant::InWords:
        return 0;
        break;
    default:
        Serial.println("[ERROR] G.minuteVariant undefined");
        return 0;
        break;
    }
}

//------------------------------------------------------------------------------

void ClockWork::showSpecialWordBeen(const uint8_t min) {
    if (usedClockType->hasSpecialWordBeen()) {
        if (min == 0) {
            usedClockType->show(FrontWord::nur);
        } else {
            usedClockType->show(FrontWord::gewesen);
        }
    }
}

//------------------------------------------------------------------------------

bool ClockWork::checkIfClockHasMinuteInWordsAndItIsSet() {
    return usedClockType->hasMinuteInWords() &&
           G.minuteVariant == MinuteVariant::InWords;
}

//------------------------------------------------------------------------------

void ClockWork::showMinuteInWords(const uint8_t min) {
    if (checkIfClockHasMinuteInWordsAndItIsSet()) {
        if (min > 0) {
            usedClockType->show(FrontWord::plus);
            usedClockType->show(FrontWord::minute);
            if (min % 5 > 1) {
                usedClockType->show(FrontWord::minuten);
            }
        }
        switch (min) {
        case 0:
            break;
        case 1:
            usedClockType->show(FrontWord::m_num1);
            break;
        case 2:
            usedClockType->show(FrontWord::m_num2);
            break;
        case 3:
            usedClockType->show(FrontWord::m_num3);
            break;
        case 4:
            usedClockType->show(FrontWord::m_num4);
            break;

        default:
            break;
        }
    }
}

//------------------------------------------------------------------------------

void ClockWork::showMinute(uint8_t min) {
    /* To prevent errors if min is not in Range of [0-4] */
    min %= 5;

    /* saving corosponding minutePixelArray */
    usedClockType->getMinuteArray(minutePixelArray,
                                  determineWhichMinuteVariant());
    /* Reseting minute byte */
    minuteArray = 0;
    if (usedClockType->hasMinuteInWords() && min > 0) {
        minuteArray |= 1UL << (min - 1);
    } else {
        for (uint8_t i = 0; i < min; i++) {
            /* Shifting a 1 Bit for every pixel starting at LSB */
            minuteArray |= 1UL << i;
        }
    }
    /* Show "Been" according to ClockTypedef */
    showSpecialWordBeen(min);

    /* Show Minute "In Words" according to ClockTypedef */
    showMinuteInWords(min);
}

//------------------------------------------------------------------------------

void ClockWork::checkForValidLanguageVariant() {
    if (G.clockTypeDef == Eng10x11) {
        G.languageVariant[ItIs15] = false;
        G.languageVariant[ItIs20] = true;
        G.languageVariant[ItIs40] = true;
    } else { // default values
        G.languageVariant[ItIs15] = false;
        G.languageVariant[ItIs20] = false;
        G.languageVariant[ItIs40] = false;
    }
}

//------------------------------------------------------------------------------

void ClockWork::resetMinVariantIfNotAvailable() {
    if (usedClockType->supportsMinuteVariant(G.minuteVariant)) {
        return;
    }

    if (G.minuteVariant == MinuteVariant::Corners &&
        usedClockType->supportsMinuteVariant(MinuteVariant::LED4x)) {
        G.minuteVariant = MinuteVariant::LED4x;
    } else {
        G.minuteVariant = MinuteVariant::Off;
    }
}

//------------------------------------------------------------------------------

FrontWord ClockWork::getFrontWordForNum(uint8_t min) {
    if (min == 0 || min > 59) {
        Serial.println("[Error] getFrontWordForNum() out of Bounds");
        return FrontWord::error;
    } else {
        return static_cast<FrontWord>(min);
    }
}

//------------------------------------------------------------------------------

bool ClockWork::checkTwentyUsage() {
    return G.languageVariant[ItIs20] || G.languageVariant[ItIs40] ||
           usedClockType->usedLang() == LanguageAbbreviation::ES ||
           usedClockType->usedLang() == LanguageAbbreviation::TR;
}

//------------------------------------------------------------------------------

bool ClockWork::hasTwentyAndCheckForUsage() {
    // ToDo: Is this true for every supoorted language variant?
    return usedClockType->hasTwenty() && checkTwentyUsage();
}

//------------------------------------------------------------------------------

bool ClockWork::hasDreiviertelAndCheckForUsage() {
    if (usedClockType->hasDreiviertel()) {
        if (usedClockType->usedLang() != LanguageAbbreviation::DE) {
            return true;
        } else if (G.languageVariant[ItIs45]) {
            return true;
        }
    }
    return false;
}

//------------------------------------------------------------------------------

void ClockWork::setMinute(uint8_t min, uint8_t &offsetHour, bool &fullHour) {
    if (usedClockType->has60MinuteLayout()) {
        usedClockType->show(FrontWord::uhr);

        if (min == 0) {
            fullHour = true;
        } else if (min > 0) {
            usedClockType->show(getFrontWordForNum(min));
            usedClockType->show(FrontWord::und);
        }

        if (min == 1) {
            usedClockType->show(FrontWord::minute);
        } else if (min > 1) {
            usedClockType->show(FrontWord::minuten);
        }
    } else if (usedClockType->hasOnlyQuarterLayout()) {

        if (8 <= min && min <= 22) {
            if (G.languageVariant[ItIs15]) {
                usedClockType->show(FrontWord::viertel);
                offsetHour = 1;
            } else {
                // A Quarter past
                if (G.languageVariant[EN_ShowAQuarter]) {
                    usedClockType->show(FrontWord::a_quarter);
                }
                usedClockType->show(FrontWord::viertel);
                usedClockType->show(FrontWord::v_nach);
            }
        } else if (23 <= min && min <= 37) { // half
            if (G.clockTypeDef == Eng10x11 || G.clockTypeDef == It10x11 ||
                G.clockTypeDef == Es10x11 || G.clockTypeDef == Ro10x11) {
                usedClockType->show(FrontWord::halb);
                usedClockType->show(FrontWord::nach);
            } else {
                if (G.clockTypeDef == Fr10x11 || G.clockTypeDef == Ru10x11) {
                    usedClockType->show(FrontWord::halb);
                } else {
                    usedClockType->show(FrontWord::halb);
                    offsetHour = 1;
                }
            }
        } else if (38 <= min && min <= 52) { // quarter to
            if (hasDreiviertelAndCheckForUsage()) {
                usedClockType->show(FrontWord::dreiviertel);
            } else {
                // A Quarter to
                if (G.languageVariant[EN_ShowAQuarter]) {
                    usedClockType->show(FrontWord::a_quarter);
                }
                usedClockType->show(FrontWord::viertel);
                usedClockType->show(FrontWord::v_vor);
            }
            offsetHour = 1;
        } else if (53 <= min && min <= 59) { // almost full hour
            offsetHour = 1;
        }
    } else {
        showMinute(min);
        min /= 5;
        min *= 5;

        switch (min) {
        case 0: // full hour
            usedClockType->show(FrontWord::uhr);
            fullHour = true;
            break;
        case 1:
            usedClockType->show(FrontWord::min_1);
            usedClockType->show(FrontWord::minute);
            usedClockType->show(FrontWord::nach);
            break;
        case 2:
        case 3:
        case 4:
        case 5:
        case 6:
        case 7:
        case 8:
        case 9:
        case 10:
            usedClockType->show(getFrontWordForNum(min));
            if (G.clockTypeDef != Fr10x11) {
                usedClockType->show(FrontWord::nach);
            }
            break;
        case 11:
        case 12:
        case 13:
        case 14:
            usedClockType->show(getFrontWordForNum(min));
            usedClockType->show(FrontWord::nach);
            break;
        case 15: // quarter past
            if (G.languageVariant[ItIs15]) {
                usedClockType->show(FrontWord::viertel);
                offsetHour = 1;
            } else {
                // A Quarter past
                if (G.languageVariant[EN_ShowAQuarter]) {
                    usedClockType->show(FrontWord::a_quarter);
                }
                usedClockType->show(FrontWord::viertel);
                usedClockType->show(FrontWord::v_nach);
            }
            break;
        case 16:
        case 17:
        case 18:
        case 19:
            usedClockType->show(getFrontWordForNum(min));
            usedClockType->show(FrontWord::nach);
            break;
        case 20:
            if (hasTwentyAndCheckForUsage()) {
                usedClockType->show(FrontWord::min_20);
                if (G.clockTypeDef != Fr10x11) {
                    usedClockType->show(FrontWord::nach);
                }
            } else {
                usedClockType->show(FrontWord::min_10);
                usedClockType->show(FrontWord::vor);
                usedClockType->show(FrontWord::halb);
                offsetHour = 1;
            }
            break;
        case 21:
        case 22:
        case 23:
        case 24:
        case 25:
            if (usedClockType->hasTwentyfive()) {
                usedClockType->show(FrontWord::min_25);
                if (G.clockTypeDef != Fr10x11) {
                    usedClockType->show(FrontWord::nach);
                }
            } else {
                usedClockType->show(FrontWord::min_5);
                usedClockType->show(FrontWord::vor);
                usedClockType->show(FrontWord::halb);
                offsetHour = 1;
            }
            break;
        case 26:
        case 27:
        case 28:
            usedClockType->show(getFrontWordForNum(30 - min));
            usedClockType->show(FrontWord::vor);
            usedClockType->show(FrontWord::halb);
            offsetHour = 1;
            break;
        case 29:
            usedClockType->show(FrontWord::min_1);
            usedClockType->show(FrontWord::minute);
            usedClockType->show(FrontWord::vor);
            usedClockType->show(FrontWord::halb);
            offsetHour = 1;
            break;
        case 30: // half
            if (G.clockTypeDef == Tr10x11) {
                usedClockType->show(FrontWord::halb);
                fullHour = true;
            } else if (G.clockTypeDef == Eng10x11 ||
                       G.clockTypeDef == Eng08x08 ||
                       G.clockTypeDef == It10x11 || G.clockTypeDef == Ro10x11 ||
                       G.clockTypeDef == Es10x11 ||
                       G.clockTypeDef == Es08x08Cuarto) {
                usedClockType->show(FrontWord::halb);
                usedClockType->show(FrontWord::nach);
            } else {
                if (G.clockTypeDef == Fr10x11 || G.clockTypeDef == Ru10x11) {
                    usedClockType->show(FrontWord::halb);
                } else {
                    usedClockType->show(FrontWord::halb);
                    offsetHour = 1;
                }
            }
            break;
        case 31:
            usedClockType->show(FrontWord::min_1);
            usedClockType->show(FrontWord::minute);
            usedClockType->show(FrontWord::nach);
            usedClockType->show(FrontWord::halb);
            offsetHour = 1;
            break;
        case 32:
        case 33:
        case 34:
        case 35:
            if (usedClockType->hasThirtyfive()) {
                usedClockType->show(FrontWord::min_35);
                usedClockType->show(FrontWord::nach);
            } else if (usedClockType->hasTwentyfive()) {
                usedClockType->show(FrontWord::min_25);
                usedClockType->show(FrontWord::vor);
                offsetHour = 1;
            } else {
                usedClockType->show(FrontWord::min_5);
                usedClockType->show(FrontWord::nach);
                usedClockType->show(FrontWord::halb);
                offsetHour = 1;
            }
            break;
        case 36:
        case 37:
        case 38:
        case 39:
            usedClockType->show(getFrontWordForNum(min - 30));
            usedClockType->show(FrontWord::nach);
            usedClockType->show(FrontWord::halb);
            offsetHour = 1;
            break;
        case 40:
            if (usedClockType->hasForty()) {
                usedClockType->show(FrontWord::min_40);
            } else if (hasTwentyAndCheckForUsage()) {
                usedClockType->show(FrontWord::min_20);
                usedClockType->show(FrontWord::vor);
            } else {
                usedClockType->show(FrontWord::min_10);
                usedClockType->show(FrontWord::nach);
                usedClockType->show(FrontWord::halb);
            }
            if (G.clockTypeDef != Tr10x11) {
                offsetHour = 1;
            }
            break;
        case 41:
        case 42:
        case 43:
        case 44:
            usedClockType->show(getFrontWordForNum(60 - min));
            usedClockType->show(FrontWord::vor);
            offsetHour = 1;
            break;
        case 45: // quarter to
            if (G.clockTypeDef == Tr10x11) {
                usedClockType->show(FrontWord::min_45);
                usedClockType->show(FrontWord::nach);
            } else if (hasDreiviertelAndCheckForUsage()) {
                usedClockType->show(FrontWord::dreiviertel);
            } else {
                // A Quarter to
                if (G.languageVariant[EN_ShowAQuarter]) {
                    usedClockType->show(FrontWord::a_quarter);
                }
                usedClockType->show(FrontWord::viertel);
                usedClockType->show(FrontWord::v_vor);
            }
            if (G.clockTypeDef != Tr10x11) {
                offsetHour = 1;
            }
            break;
        case 46:
        case 47:
        case 48:
        case 49:
        case 50:
            if (usedClockType->hasFifty()) {
                usedClockType->show(FrontWord::min_50);
            } else {
                usedClockType->show(getFrontWordForNum(60 - min));
                usedClockType->show(FrontWord::vor);
            }
            if (G.clockTypeDef != Tr10x11) {
                offsetHour = 1;
            }
            break;
        case 51:
        case 52:
        case 53:
        case 54:
        case 55:
            if (usedClockType->hasFiftyFive()) {
                usedClockType->show(FrontWord::min_55);
            } else {
                usedClockType->show(getFrontWordForNum(60 - min));
                usedClockType->show(FrontWord::vor);
            }
            if (G.clockTypeDef != Tr10x11) {
                offsetHour = 1;
            }
            break;
        case 56:
        case 57:
        case 58:
            usedClockType->show(getFrontWordForNum(60 - min));
            usedClockType->show(FrontWord::minuten);
            usedClockType->show(FrontWord::vor);
            offsetHour = 1;
            break;
        case 59:
            usedClockType->show(FrontWord::min_1);
            usedClockType->show(FrontWord::minute);
            usedClockType->show(FrontWord::vor);
            offsetHour = 1;
            break;
        default:
            break;
        }

        if (G.clockTypeDef == Ru10x11) {
            offsetHour = 0;
        }
    }
}

//------------------------------------------------------------------------------
// Hour Functions
//------------------------------------------------------------------------------

void ClockWork::setHour(uint8_t hour, const bool fullHour) {
    bool midnight = isMidnight(hour);

    if (!usedClockType->has24HourLayout()) {
        hour %= 12;
    }

    bool turkishBaseHour =
        usedClockType->usedLang() == LanguageAbbreviation::TR && fullHour;
    if (turkishBaseHour && hour != 0) {
        hour += 12;
    }

    switch (hour) {
    case 0:
        if (turkishBaseHour) {
            usedClockType->show(FrontWord::hour_0);
        } else if (midnight) {
            usedClockType->show(FrontWord::hour_0);
        } else {
            usedClockType->show(FrontWord::hour_12);
        }
        break;
    case 1:
        if (fullHour || usedClockType->usedLang() != LanguageAbbreviation::DE) {
            usedClockType->show(FrontWord::hour_1);
        } else {
            usedClockType->show(FrontWord::eins);
        }
        break;
    case 2:
        usedClockType->show(FrontWord::hour_2);
        break;
    case 3:
        usedClockType->show(FrontWord::hour_3);
        break;
    case 4:
        usedClockType->show(FrontWord::hour_4);
        break;
    case 5:
        usedClockType->show(FrontWord::hour_5);
        break;
    case 6:
        usedClockType->show(FrontWord::hour_6);
        break;
    case 7:
        usedClockType->show(FrontWord::hour_7);
        break;
    case 8:
        usedClockType->show(FrontWord::hour_8);
        break;
    case 9:
        usedClockType->show(FrontWord::hour_9);
        break;
    case 10:
        usedClockType->show(FrontWord::hour_10);
        break;
    case 11:
        usedClockType->show(FrontWord::hour_11);
        break;
    case 12:
        usedClockType->show(FrontWord::hour_12);
        break;
    case 13:
        usedClockType->show(FrontWord::hour_13);
        break;
    case 14:
        usedClockType->show(FrontWord::hour_14);
        break;
    case 15:
        usedClockType->show(FrontWord::hour_15);
        break;
    case 16:
        usedClockType->show(FrontWord::hour_16);
        break;
    case 17:
        usedClockType->show(FrontWord::hour_17);
        break;
    case 18:
        usedClockType->show(FrontWord::hour_18);
        break;
    case 19:
        usedClockType->show(FrontWord::hour_19);
        break;
    case 20:
        usedClockType->show(FrontWord::hour_20);
        break;
    case 21:
        usedClockType->show(FrontWord::hour_21);
        break;
    case 22:
        usedClockType->show(FrontWord::hour_22);
        break;
    case 23:
        usedClockType->show(FrontWord::hour_23);
        break;

    default:
        break;
    }
}

//------------------------------------------------------------------------------
// Loop Helper Functions
//------------------------------------------------------------------------------

bool ClockWork::isMidnight(const uint8_t hour) {
    return usedClockType->hasMitternacht() && hour == 0;
}

//------------------------------------------------------------------------------

WordclockChanges ClockWork::changesInClockface() {
    for (uint16_t i = 0; i < MAX_ROW_SIZE; i++) {
        if (frontMatrix[i] != lastFrontMatrix[i]) {
            return WordclockChanges::Words;
        }
    }
    if (parametersChanged) {
        parametersChanged = false;
        return WordclockChanges::Parameters;
    } else if (layoutChanged) {
        layoutChanged = false;
        return WordclockChanges::Layout;
    } else if (lastMinuteArray != minuteArray) {
        return WordclockChanges::Minute;
    }
    return WordclockChanges::Null;
}

//------------------------------------------------------------------------------

bool ClockWork::DetermineIfItIsIsShown(const uint8_t min) {
    switch (G.itIsVariant) {
    case ItIsVariant::Permanent:
        return true;
    case ItIsVariant::Hourly:
        return !min;
    case ItIsVariant::HalfHourly:
        return !(min % 30);
    case ItIsVariant::Quarterly:
        return !(min % 15);
    case ItIsVariant::Off:
    default:
        return false;
    }
}

//------------------------------------------------------------------------------
void ClockWork::setItIs(uint8_t min, const uint8_t offsetHour) {
    min /= 5;
    min *= 5;

    if (DetermineIfItIsIsShown(min)) {
        DetermineWhichItIsToShow(_hour + offsetHour, min);
    }
}

//------------------------------------------------------------------------------

void ClockWork::setClock() {
    uint8_t offsetHour = 0;
    bool fullHour = 0;

    setMinute(_minute, offsetHour, fullHour);
    setHour(_hour + offsetHour, fullHour);
    setDaytimeWords(_hour + offsetHour);
    setItIs(_minute, offsetHour);
}

//------------------------------------------------------------------------------

void ClockWork::setDaytimeWords(uint8_t hour) {
    if (!usedClockType->hasDaytimeWords()) {
        return;
    }

    hour %= 24;

    if (hour == 0) {
        usedClockType->show(FrontWord::mitternachts);
    } else if (hour < 5) {
        usedClockType->show(FrontWord::day_night);
    } else if (hour < 10) {
        usedClockType->show(FrontWord::day_morning);
        usedClockType->show(FrontWord::day_early);
    } else if (hour < 12) {
        usedClockType->show(FrontWord::day_morning);
    } else if (hour < 14) {
        usedClockType->show(FrontWord::day_noon);
    } else if (hour >= 18) {
        usedClockType->show(FrontWord::day_evening);
    }
}

//------------------------------------------------------------------------------

void ClockWork::DetermineWhichItIsToShow(uint8_t hour, uint8_t min) {
    hour %= 12;
    if (G.clockTypeDef == Ru10x11) {
        switch (hour) {
        case 1:
            usedClockType->show(FrontWord::es_ist__singular__);
            break;
        case 2:
        case 3:
        case 4:
            usedClockType->show(FrontWord::es_ist___plural___);
            break;
        default:
            usedClockType->show(FrontWord::es_ist);
            break;
        }
    } else if (G.clockTypeDef == Es10x11 && hour == 1 && min < 35) {
        usedClockType->show(FrontWord::es_ist___plural___);
    } else if (G.clockTypeDef == Es10x11 && hour == 0 && min > 34) {
        usedClockType->show(FrontWord::es_ist___plural___);
    } else {
        usedClockType->show(FrontWord::es_ist);
    }
}

//------------------------------------------------------------------------------

void ClockWork::calcClockface() {
    led.resetFrontMatrixBuffer();

    if (_hour == 23 && _minute == 59 && _second >= 50) {
        countdownToMidnight();
    } else {
        setClock();
    }

    if (usedClockType->hasWeatherLayout()) {
        weather.calcWeatherClockface();
    }
}

//------------------------------------------------------------------------------

void ClockWork::clearClockByProgInit() {
    if (G.progInit) {
        G.progInit = false;
        led.clear();
        led.show();
    }
}

//------------------------------------------------------------------------------
// Loop Functions
//------------------------------------------------------------------------------

void ClockWork::loop(struct tm &tm) {
    unsigned long currentMillis = millis();
    countMillisSpeed += currentMillis - previousMillis;
    previousMillis = currentMillis;
    loopHardwareButtons();

    // Faster runtime for demo
    transition->demoMode(_hour, _minute, _second);

    //------------------------------------------------
    // Seconds and LDR Routine
    //------------------------------------------------
    if (lastSecond != _second) {

#if GENERAL_VERBOSE
        char currentTime[80];
        strftime(currentTime, sizeof(currentTime), "%F %T (%z)\n", &tm);
        Serial.printf(currentTime);
#endif

        //--------------------------------------------
        // Weather Loop
        //--------------------------------------------
        if (usedClockType->hasWeatherLayout()) {
            weather.loop();
        }

        //--------------------------------------------
        // Auto Brightness Logic
        //--------------------------------------------
        if (G.autoBrightEnabled == 1) {
            loopAutoBrightLogic();
        }

        if (G.prog == COMMAND_IDLE && G.conf == COMMAND_IDLE) {
            led.clear();
            G.prog = COMMAND_MODE_WORD_CLOCK;
        }

        if (G.prog == COMMAND_MODE_DIGITAL_CLOCK) {
            led.clear();
            led.showDigitalClock(_minute % 10, _minute / 10, _hour % 10,
                                 _hour / 10);
        }

        lastSecond = _second;
    }

    //------------------------------------------------
    // Minute
    //------------------------------------------------
    if (lastMinute != _minute) {
        lastMinute = _minute;
        if (colorChangedByWebsite) {
            eeprom::write();
            colorChangedByWebsite = false;
            Serial.println("Saved Color");
        }

        //------------------------------------------------
        // MQTT
        //------------------------------------------------

        sendMQTTUpdate();
    }

    switch (G.conf) {

    case COMMAND_RESET: {
        delay(500);
#ifdef ESP8266
        ESP.reset();
        ESP.restart();
#elif defined(ESP32)
        ESP.restart();
        esp_restart();
#endif
        while (true) {
        }
        break;
    }

    case COMMAND_REQUEST_MQTT_VALUES: {
        DynamicJsonDocument config(512);
        config["command"] = "mqtt";
        config["MQTT_State"] = G.mqtt.state;
        config["MQTT_Port"] = G.mqtt.port;
        config["MQTT_Server"] = G.mqtt.serverAdress;
        config["MQTT_User"] = G.mqtt.user;

        // don't expose password:
        char passMasked[sizeof(G.mqtt.password) + 1] = {0};
        sensitive::maskPreservingSuffix(passMasked, G.mqtt.password);
        config["MQTT_Pass"] = passMasked;

        config["MQTT_ClientId"] = G.mqtt.clientId;
        config["MQTT_Topic"] = G.mqtt.topic;

        sendJsonToClient(G.client_nr, config);
        break;
    }

    case COMMAND_REQUEST_CONFIG_VALUES: {
        DynamicJsonDocument config(1280);
        config["command"] = "config";
        config["ssid"] = network.getSSID();
        config["timeserver"] = G.timeserver;
        config["timezone"] = G.timezone;
        config["hostname"] = G.hostname;
        config["scrollingText"] = G.scrollingText;
        config["h6"] = G.h6;
        config["h8"] = G.h8;
        config["h12"] = G.h12;
        config["h16"] = G.h16;
        config["h18"] = G.h18;
        config["h20"] = G.h20;
        config["h22"] = G.h22;
        config["h24"] = G.h24;
        for (uint8_t i = 0;
             i < sizeof(G.languageVariant) / sizeof(G.languageVariant[0]);
             i++) {
            char string2Send[11];
            sprintf(string2Send, "langVar%d", i);
            config[string2Send] = static_cast<uint8_t>(G.languageVariant[i]);
        }
        for (uint8_t i = 0;
             i < sizeof(G.layoutVariant) / sizeof(G.layoutVariant[0]); i++) {
            char string2Send[11];
            sprintf(string2Send, "layVar%d", i);
            config[string2Send] = static_cast<uint8_t>(G.layoutVariant[i]);
        }
        config["effectBri"] = G.effectBri;
        config["itIsVariant"] = static_cast<uint8_t>(G.itIsVariant);
        config["secondVariant"] = static_cast<uint8_t>(G.secondVariant);
        config["minuteVariant"] = static_cast<uint8_t>(G.minuteVariant);
        config["supportedMinuteVariants"] =
            usedClockType->supportedMinuteVariantMask();
        config["cityid"] = G.openWeatherMap.cityid;
        char apiKeyMasked[sizeof(G.openWeatherMap.apikey) + 1] = {0};
        sensitive::maskPreservingSuffix(apiKeyMasked, G.openWeatherMap.apikey);
        config["apiKey"] = apiKeyMasked;
        config["colortype"] = G.Colortype;
        config["buildtype"] = static_cast<uint8_t>(G.buildTypeDef);
        config["wType"] = static_cast<uint8_t>(G.wType);
        config["clockTypeDef"] = G.clockTypeDef;
        config["bitmapSymbol"] = static_cast<uint8_t>(G.bitmapSymbol);
        config["bootLedBlink"] = G.bootLedBlink;
        config["bootLedSweep"] = G.bootLedSweep;
        config["bootShowWifi"] = G.bootShowWifi;
        config["bootShowIP"] = G.bootShowIP;
        config["ledPin"] = G.hardwarePins.led;
        config["powerButtonPin"] = G.hardwarePins.powerButton;
        config["modeButtonPin"] = G.hardwarePins.modeButton;
        config["speedButtonPin"] = G.hardwarePins.speedButton;
        config["i2cSdaPin"] = G.i2cSdaPin;
        config["i2cSclPin"] = G.i2cSclPin;
        config["autoBrightEnabled"] = G.autoBrightEnabled;
        config["isRomanLanguage"] = usedClockType->isRomanLanguage();
        config["hasDreiviertel"] = usedClockType->hasDreiviertel();
        config["hasTwenty"] = usedClockType->hasTwenty();
        config["hasWeatherLayout"] = usedClockType->hasWeatherLayout();
        config["hasSecondsFrame"] = usedClockType->hasSecondsFrame();
        config["hasMinuteInWords"] = usedClockType->hasMinuteInWords();
        config["hasSpecialWordHappyBirthday"] =
            usedClockType->hasSpecialWordHappyBirthday();
        config["numOfRows"] = usedClockType->rowsWordMatrix();

        sendJsonToClient(G.client_nr, config);
        break;
    }

    case COMMAND_REQUEST_BIRTHDAYS: {
        DynamicJsonDocument config(256);
        config["command"] = "birthdays";
        config["hasSpecialWordHappyBirthday"] =
            usedClockType->hasSpecialWordHappyBirthday();
        for (uint8_t i = 0; i < MAX_BIRTHDAY_COUNT; i++) {
            char dateString[10];
            char string2Send[16];
            snprintf(string2Send, sizeof(string2Send), "birthdayDate%d", i);
            snprintf(dateString, sizeof(dateString), "%02u-%02u",
                     G.birthday[i].month, G.birthday[i].day);
            config[string2Send] = dateString;
        }

        sendJsonToClient(G.client_nr, config);
        break;
    }

    case COMMAND_REQUEST_I2C_SCAN: {
        sendI2CScanResult(G.client_nr, i2cScanSdaPin, i2cScanSclPin);
        break;
    }

    case COMMAND_REQUEST_COLOR_VALUES: {
        DynamicJsonDocument config(768);
        config["command"] = "set";
        for (uint8_t i = 0; i < 3; i++) {
            char string2Send[7];
            sprintf(string2Send, "hsb%d%d", i, 0);
            config[string2Send] = static_cast<uint16_t>(G.color[i].H * 360);
            sprintf(string2Send, "hsb%d%d", i, 1);
            config[string2Send] = static_cast<uint8_t>(G.color[i].S * 100);
            sprintf(string2Send, "hsb%d%d", i, 2);
            config[string2Send] = static_cast<uint8_t>(G.color[i].B * 100);
        }
        config["effectBri"] = G.effectBri;
        config["effectSpeed"] = G.effectSpeed;
        config["colortype"] = G.Colortype;
        config["hasSpecialWordHappyBirthday"] =
            usedClockType->hasSpecialWordHappyBirthday();
        config["hasSecondsFrame"] = usedClockType->hasSecondsFrame();
        config["prog"] = G.prog;
        config["bitmapSymbol"] = static_cast<uint8_t>(G.bitmapSymbol);

        sendJsonToClient(G.client_nr, config);
        break;
    }

    case COMMAND_REQUEST_AUTO_BRIGHT: {
        DynamicJsonDocument config(256);
        config["command"] = "autoBright";
        config["autoBrightEnabled"] = G.autoBrightEnabled;
        if (G.param1 == 1) {
            config["autoBrightMin"] = G.autoBrightMin;
            config["autoBrightMax"] = G.autoBrightMax;
            config["autoBrightPeak"] = G.autoBrightPeak;
        }
        config["autoBrightSensor"] = (uint32_t)lux;
        config["autoBrightGain"] = (uint8_t)ledGain;
        config["autoBrightSource"] = autoBrightUsingBH1750 ? "BH1750" : "LDR";

        sendJsonToClient(G.client_nr, config);
        break;
    }

    case COMMAND_REQUEST_TRANSITION: {
        DynamicJsonDocument config(256);
        config["command"] = "transition";
        config["transitionType"] = G.transitionType;
        config["transitionDuration"] = G.transitionDuration;
        config["transitionSpeed"] = G.transitionSpeed;
        config["transitionDemo"] = G.transitionDemo;
        config["transitionColorize"] = G.transitionColorize;

        sendJsonToClient(G.client_nr, config);
        break;
    }

    case COMMAND_SET_BIRTHDAYS:
    case COMMAND_SET_TIME:
    case COMMAND_SET_INITIAL_VALUES:
    case COMMAND_SET_WEATHER_DATA:
    case COMMAND_SET_SCROLLINGTEXT:
    case COMMAND_SET_TIMESERVER:
    case COMMAND_SET_BOOT: {
        eeprom::write();
        delay(100);
        break;
    }

    case COMMAND_SET_TIMEZONE: {
        applyTimezone();
        eeprom::write();
        parametersChanged = true;
        delay(100);
        break;
    }

    case COMMAND_SET_BUILDTYPE: {
        led.clear();

        // G.param1 sets new buildtype
        Serial.printf("Clock Buildtype: %u\n", G.param1);

        G.buildTypeDef = static_cast<BuildTypeDef>(G.param1);
        eeprom::write();
        led.clear();
        parametersChanged = true;
        break;
    }

    case COMMAND_SET_MINUTE:
        resetMinVariantIfNotAvailable();
        eeprom::write();
        led.clear();
        memset(frameArray, false, sizeof(frameArray));
        parametersChanged = true;
        break;

    case COMMAND_SET_BRIGHTNESS:
    case COMMAND_SET_AUTO_BRIGHT:
    case COMMAND_SET_WHITETYPE:
    case COMMAND_SET_TIME_MANUAL:
    case COMMAND_SET_LAYOUT_VARIANT: {
        eeprom::write();
        led.clear();
        memset(frameArray, false, sizeof(frameArray));
        parametersChanged = true;
        break;
    }

    case COMMAND_SET_LANGUAGE_VARIANT:
    case COMMAND_SET_SETTING_SECOND: {
        eeprom::write();
        led.clear();
        G.progInit = true;
        parametersChanged = true;
        break;
    }

    case COMMAND_SET_MQTT: {
        if (G.mqtt.state && G.progInit) {
            mqtt.init();
            G.progInit = false;
        }
        delay(100);

        eeprom::write();
        break;
    }

    case COMMAND_SET_MQTT_HA_DISCOVERY: {
        mqtt.sendDiscovery();
        break;
    }

    case COMMAND_SET_HARDWARE_PINS: {
        if (!hardwarePinsAreValid()) {
            Serial.println("Invalid hardware pin configuration, restoring "
                           "defaults");
            setDefaultHardwarePins();
            i2cBus::setDefaultPins(G.i2cSdaPin, G.i2cSclPin);
        }

        Serial.printf("Hardware LED pin: GPIO%u\n", G.hardwarePins.led);
        Serial.printf("Hardware power button pin: GPIO%u\n",
                      G.hardwarePins.powerButton);
        Serial.printf("Hardware mode button pin: GPIO%u\n",
                      G.hardwarePins.modeButton);
        Serial.printf("Hardware speed button pin: GPIO%u\n",
                      G.hardwarePins.speedButton);
        Serial.printf("I2C SDA pin: GPIO%u\n", G.i2cSdaPin);
        Serial.printf("I2C SCL pin: GPIO%u\n", G.i2cSclPin);

        eeprom::write();
        i2cBus::begin(G.i2cSdaPin, G.i2cSclPin);
        initHardwareButtons();
        initLedStrip(G.Colortype);
        led.clear();
        parametersChanged = true;
        break;
    }

    case COMMAND_SET_COLORTYPE: {
        // G.param1 sets new Colortype
        Serial.printf("LED Colortype: %u\n", G.param1);

        // the G.Colortype must be called at the same time as initLedStrip,
        // otherwise it is referenced via a null-pointer.
        G.Colortype = G.param1;
        eeprom::write();
        initLedStrip(G.Colortype);

        clearClockByProgInit();
        parametersChanged = true;
        break;
    }

    case COMMAND_SET_CLOCK_TYPE: {
        if (!isValidClockTypeDef(G.clockTypeDef)) {
            Serial.printf("Ignoring invalid ClockType: %u\n", G.clockTypeDef);
            break;
        }

        eeprom::write();
        led.clear();
        led.show();
        delay(10);
        Serial.printf("ClockType: %u\n", G.clockTypeDef);

        usedClockType = getPointer(G.clockTypeDef);
        resetMinVariantIfNotAvailable();

        checkForValidLanguageVariant();

        delete secondsFrame;
        secondsFrame = nullptr;

        if (usedClockType->numPixelsFrameMatrix() != 0) {
            secondsFrame =
                new SecondsFrame(usedClockType->numPixelsFrameMatrix());
            G.progInit = true;
        }

        transition->resize(usedClockType->rowsWordMatrix(),
                           usedClockType->colsWordMatrix());
        transition->init();

        parametersChanged = true;
        break;
    }

    case COMMAND_SET_HOSTNAME: {
        Serial.print("Hostname: ");
        Serial.println(G.hostname);
        eeprom::write();
        network.reboot();
        break;
    }

    case COMMAND_SET_WIFI_DISABLED: {
        eeprom::write();
        delay(100);
        Serial.println("Conf: WLAN off");
        network.disable();
        break;
    }

    case COMMAND_SET_WIFI_AND_RESTART: {
        Serial.println("Conf: new Wifi Config");
        network.resetSettings();
        break;
    }

    default:
        break;
    }

    G.conf = COMMAND_IDLE;

    switch (G.prog) {

    case COMMAND_MODE_SECONDS: {
        // 0xFF marks "nothing drawn yet" and cannot collide with a second.
        static uint8_t lastShownSecond = 0xFF;

        if (G.progInit) {
            clearClockByProgInit();
            lastShownSecond = 0xFF;
        }

        // This runs on every loop() iteration. Without this guard the LED
        // strip is rewritten thousands of times per second, which starves the
        // network stack -- the display only ever changes once per second.
        if (lastShownSecond == _second && !parametersChanged) {
            break;
        }
        lastShownSecond = _second;
        parametersChanged = false;

        char d1[5];
        char d2[5];
        sprintf(d1, "%d", static_cast<uint8_t>(_second / 10));
        sprintf(d2, "%d", static_cast<uint8_t>(_second % 10));
        led.showNumbers(d1[0], d2[0]);
        break;
    }

    case COMMAND_MODE_DIGITAL_CLOCK: {
        if (G.progInit) {
            clearClockByProgInit();
        }
        if (parametersChanged) {
            led.showDigitalClock(_minute % 10, _minute / 10, _hour % 10,
                                 _hour / 10);
            parametersChanged = false;
        }
        break;
    }

    case COMMAND_MODE_SCROLLINGTEXT:
    case COMMAND_MODE_RAINBOWCYCLE:
    case COMMAND_MODE_RAINBOW:
    case COMMAND_MODE_SYMBOL: {
        if (G.progInit) {
            countMillisSpeed = (11u - G.effectSpeed) * 30u;
            clearClockByProgInit();
        }

        if (countMillisSpeed >= (11u - G.effectSpeed) * 30u) {
            switch (G.prog) {
            case COMMAND_MODE_SCROLLINGTEXT: {
                scrollingText(G.scrollingText);
                break;
            }
            case COMMAND_MODE_RAINBOWCYCLE: {
                rainbowCycle();
                break;
            }
            case COMMAND_MODE_RAINBOW: {
                rainbow();
                break;
            }
            case COMMAND_MODE_SYMBOL: {
                displaySymbols(G.bitmapSymbol);
                break;
            }
            default:
                break;
            }
            countMillisSpeed = 0;
        }
        break;
    }

    case COMMAND_MODE_COLOR: {
        if (G.progInit) {
            clearClockByProgInit();
            for (uint8_t row = 0; row < usedClockType->rowsWordMatrix();
                 row++) {
                frontMatrix[row] = num32BitWithOnesAccordingToColumns();
            }
        }

        if (parametersChanged) {
            led.setbyFrontMatrix(Foreground, false);
            led.show();
            parametersChanged = false;
        }
        break;
    }

    case COMMAND_MODE_TRANSITION: {
        if (G.progInit) {
            G.progInit = false;
            eeprom::write();
            delay(100);
        }
        // There is no break here on purpose, directly after the call
        // COMMAND_MODE_TRANSITION, COMMAND_MODE_WORD_CLOCK must be called
    }

    case COMMAND_MODE_WORD_CLOCK: {
        clearClockByProgInit();
        calcClockface();

        switch (changesInClockface()) {
        case WordclockChanges::Minute:
            lastMinuteArray = minuteArray;
            memcpy(&lastFrontMatrix, &frontMatrix, sizeof lastFrontMatrix);
            led.set(WordclockChanges::Minute);
            break;
        case WordclockChanges::Words:
            lastMinuteArray = minuteArray;
            memcpy(&lastFrontMatrix, &frontMatrix, sizeof lastFrontMatrix);
            led.set(WordclockChanges::Words);
            break;
        case WordclockChanges::Layout:
            led.set(WordclockChanges::Layout);
            break;
        case WordclockChanges::Parameters:
            led.set(WordclockChanges::Parameters);
            break;
        default:
            break;
        }
        G.prog = COMMAND_IDLE;
    }
    default:
        break;
    }

    if (countMillisSpeed > 10000) {
        countMillisSpeed = 0;
    }
}
