ESPWortuhr/Multilayout-ESP-Wordclock/include/TransitionTypes/Transition.hpp

#include "Transition.h"
#include "WordClockState.h"
#include <Arduino.h>

#define STRIPE NULL
#define MAX_RANDOM 10

void Transition::allocate(uint8_t rows, uint8_t cols) {
    maxRows = rows;
    maxCols = cols;
    sizeofColumn = cols * sizeof(RgbfColor);
    old = new RgbfColor *[rows];
    act = new RgbfColor *[rows];
    work = new RgbfColor *[rows];
    for (uint8_t row = 0; row < rows; row++) {
        old[row] = new RgbfColor[cols];
        act[row] = new RgbfColor[cols];
        work[row] = new RgbfColor[cols];
    }
    rain = new Rain[cols];
    balls = new Ball[cols];
    for (uint8_t col = 0; col < cols; col++) {
        rain[col] = Rain(rows, cols);
        balls[col] = Ball(rows);
    }
    snake = new Snake(rows, cols);
    firework = new Firework(rows, cols);
}

//------------------------------------------------------------------------------

void Transition::release() {
    for (uint8_t row = 0; row < maxRows; row++) {
        delete[] old[row];
        delete[] act[row];
        delete[] work[row];
    }
    delete[] old;
    delete[] act;
    delete[] work;
    delete[] rain;
    delete[] balls;
    delete snake;
    delete firework;

    old = nullptr;
    act = nullptr;
    work = nullptr;
    rain = nullptr;
    balls = nullptr;
    snake = nullptr;
    firework = nullptr;
    maxRows = 0;
    maxCols = 0;
    sizeofColumn = 0;
}

//------------------------------------------------------------------------------

Transition::Transition(uint8_t rows, uint8_t cols) {
    allocate(rows, cols);
    transitionType = (Transition_t)G.transitionType;
    lastTransitionType = (Transition_t)G.transitionType;
    lastTransitionDemo = G.transitionDemo;
    lastTransitionDuration = G.transitionDuration;
    lastTransitionColorize = G.transitionColorize;
}

//------------------------------------------------------------------------------

Transition::~Transition() { release(); }

//------------------------------------------------------------------------------

void Transition::resize(uint8_t rows, uint8_t cols) {
    if (rows == maxRows && cols == maxCols) {
        // Same geometry (e.g. Ger10x11 -> Ger10x11Nero): keep the buffers so
        // the running animation is not interrupted.
        return;
    }

    release();
    allocate(rows, cols);

    // Drop a running animation: its phase counter refers to the old geometry.
    phase = 0;
    matrixChanged = false;
}

//------------------------------------------------------------------------------

bool isBirthday(struct tm &tm) {
    // tm_mday=1..31, tm.tm_mon=0=Jan..11=Dec, tm_year=0=1900..n=1900+n

    for (uint8_t i = 0; i < MAX_BIRTHDAY_COUNT; i++) {
        if ((G.birthday[i].month == tm.tm_mon + 1) &&
            (G.birthday[i].day == tm.tm_mday)) {
            return true;
        }
    }
    return false;
}

//------------------------------------------------------------------------------

bool isNewYear(struct tm &tm) {
    return (tm.tm_mon == 11) && (tm.tm_mday == 31) && (tm.tm_hour == 23) &&
           (tm.tm_min == 59);
}

//------------------------------------------------------------------------------

bool isSpecialEventTransition(Transition_t &type) {
    return (type == NEWYEAR_COUNTDOWN) || (type == NEWYEAR_FIRE) ||
           (type == BIRTHDAY);
}

//------------------------------------------------------------------------------
// Make special events at silvester and birthday
//------------------------------------------------------------------------------
// On Silvester, make a countdwon for the last minute of the year, then make a
// fireworks animation. On birthdays, a fireworks animation appears every 5
// minutes. Compatible clock types will display the words “Happy Birthday”
// instead of the time during the animation. Birthdays before 1900 are not
// animated.

bool Transition::isSpecialEvent(Transition_t &type, struct tm &tm,
                                bool trigger) {
    static uint8_t minutesAfterMidnight;

    if (trigger) {
        if (!isSpecialEventTransition(type)) {
            // Start only new special events when no SE is pending Conditions to
            // start a special events
            if (isNewYear(tm)) {
                minutesAfterMidnight = 0;
                type = NEWYEAR_COUNTDOWN;
            } else if (isBirthday(tm) && (tm.tm_min % 5 == 2)) {
                // Make animation 2 minutes after each clock change
                type = BIRTHDAY;
            }
        } else {
            // State machine for animation sequences
            if (type == NEWYEAR_COUNTDOWN) {
                type = NEWYEAR_FIRE;
                // after one minute countdown, switch to fireworks
            } else if (type == NEWYEAR_FIRE) {
                minutesAfterMidnight++;
                if (minutesAfterMidnight >= 10) {
                    type = getTransitionType(true);
                    // go back to standard transition
                }
            } else if (type == BIRTHDAY) {
                type = getTransitionType(true);
                // after one minute go back to standard transition
            }
        }
    }

    return isSpecialEventTransition(type);
}

//------------------------------------------------------------------------------
// Get configured transition type: Random or Fix type

Transition_t Transition::getTransitionType(bool trigger) {
    if (G.transitionType == RANDOM) {
        if (trigger) {
            return (Transition_t)random(transitionTypeFirst,
                                        transitionTypeLast + 1);
        } else {
            return transitionType;
        }
    }
    return (Transition_t)G.transitionType;
}

//------------------------------------------------------------------------------
bool Transition::isColorization() {
    return (transitionType != NO_TRANSITION && G.transitionColorize);
}

//------------------------------------------------------------------------------

bool Transition::changeBrightness() {
    RgbfColor newForeground, newBackground;
    // determine only foreground and background from LED stripe
    analyzeColors(NULL, STRIPE, newForeground, newBackground);
    bool adjustFg = newForeground != foreground,
         adjustBg = newBackground != background;

    if (adjustFg || adjustBg) {
        HsbColor hsbColor;
        float brightness = HsbColor(newForeground).B;
        hsbColor = HsbColor(foregroundMinute);
        hsbColor.B = brightness;
        foregroundMinute = RgbColor(hsbColor);
        RgbfColor **matrix[3] = {act, old, work};
        for (uint8_t m = 0; m < 3; m++) {
            for (uint8_t row = 0; row < maxRows; row++) {
                for (uint8_t col = 0; col < maxCols; col++) {
                    if (adjustBg) {
                        if (!matrix[m][row][col].isForeground()) {
                            matrix[m][row][col] = newBackground;
                        }
                    }
                    if (adjustFg) {
                        if (matrix[m][row][col].isForeground()) {
                            if (isColorization()) {
                                hsbColor = HsbColor(matrix[m][row][col]);
                                hsbColor.B = brightness;
                                matrix[m][row][col].changeRgb(hsbColor);
                            } else {
                                matrix[m][row][col].changeRgb(newForeground);
                            }
                        }
                    }
                }
            }
        }
        background = newBackground;
        foreground = newForeground;
    }
    return (adjustFg || adjustBg);
}

//------------------------------------------------------------------------------
// returns hue values with a difference of at least 0.1 (360 * 0,1 = 36 degree)
// avoiding neighbors with very similar colors

float Transition::pseudoRandomHue() {
    static bool first = true;
    if (first) {
        first = false;
        return pseudoRandomHue(true);
    }
    return pseudoRandomHue(false);
}

//------------------------------------------------------------------------------

float Transition::pseudoRandomHue(bool init) {
    static uint16_t lastColors[MAX_RANDOM];
    static uint16_t lastColor = 1000;
    static uint8_t inUse = 1;
    uint16_t hue;
    uint32_t i, tries;

    if (init || (inUse == (MAX_RANDOM - 1))) {
        inUse = 1;
        lastColors[0] = lastColor;
        for (i = 1; i < MAX_RANDOM; i++) {
            lastColors[i] = 9999;
        }
    }
    hue = 1000 + random(1000); // 1000 ... 2000
    tries = i = 0;
    do {
        if (lastColors[i] == 9999) { // empty array element
            inUse = i;
            lastColor = lastColors[i] = hue;
            return (static_cast<float>(hue - 1000)) / 1000.0; // 0.0 ... 1.0
        }
        if (((hue > (lastColors[i] - 100)) && (hue < (lastColors[i] + 100)))) {
            // hue matches an existing color, try new hue
            hue = 1000 + random(1000);
            tries++;
            i = 0;
        } else {
            // check next array element
            i++;
        }
    } while ((i < MAX_RANDOM) && (tries < 20));
    return pseudoRandomHue(true);
}

//------------------------------------------------------------------------------
// colorize foreground

void Transition::colorize(RgbfColor **dest) {
    bool changeColor = true;
    HsbColor hsbColor = HsbColor(foreground);
    hsbColor.H = pseudoRandomHue();
    foregroundMinute = isColorization() ? RgbColor(hsbColor) : foreground;
    hsbColor.H = pseudoRandomHue();
    for (uint8_t row = 0; row < maxRows; row++) {
        for (uint8_t col = 0; col < maxCols; col++) {
            if (dest[row][col].isForeground()) {
                if ((G.transitionColorize == CHARACTERS) || changeColor) {
                    changeColor = false;
                    hsbColor.H = pseudoRandomHue();
                }
                dest[row][col].changeRgb(isColorization() ? hsbColor
                                                          : foreground);
            } else {
                changeColor = true;
            }
        }
    }

    // correct color of NACH and ZWEI due non horizontal alignment
    if (G.clockTypeDef == Ger08x08 && (G.transitionColorize != CHARACTERS)) {
        // set color of VOR (if FÜNFZEHN is colored it's the same)
        if (dest[1][0].isForeground()) {
            hsbColor.H = pseudoRandomHue();
            dest[1][0].changeRgb(isColorization() ? hsbColor : foreground);
            dest[1][1] = dest[1][0];
            dest[1][2] = dest[1][0];
        }
        // set color of EINS
        if (dest[1][7].isForeground()) {
            dest[1][7] = dest[2][7];
            dest[3][7] = dest[2][7];
            dest[4][7] = dest[2][7];
        }
        // set color of ZWEI
        if (dest[7][0].isForeground()) {
            dest[6][0] = dest[7][0];
            dest[6][1] = dest[7][0];
            dest[7][1] = dest[7][0];
        }
        // set color of DREI
        if (dest[2][4].isForeground()) {
            hsbColor.H = pseudoRandomHue();
            dest[2][4].changeRgb(isColorization() ? hsbColor : foreground);
            dest[2][5] = dest[2][4];
            dest[2][6] = dest[2][4];
            dest[2][7] = dest[2][4];
        }
    }

    // correct color of NACH and ZWEI due non horizontal alignment
    if (G.clockTypeDef == Ger08x08Viertel &&
        (G.transitionColorize != CHARACTERS)) {
        // set color of A for N, C and H (A has no other word before, compared
        // to N (VIERTEL) and C (NEUN))
        if (dest[1][7].isForeground()) {
            dest[0][7] = dest[1][7];
            dest[2][7] = dest[1][7];
            dest[3][7] = dest[1][7];
        }
        // set color of Z, W for E and I if E and I are active (Z and W is also
        // used for ZWÖLF)
        if (dest[5][0].isForeground() && dest[5][1].isForeground()) {
            dest[5][0] = dest[4][0];
            dest[5][1] = dest[4][1];
        }
    }

    // correct color of DOCE and CUARTO due non horizontal alignment
    if (G.clockTypeDef == Es08x08Cuarto &&
        (G.transitionColorize != CHARACTERS)) {
        // set color of D for O, C and E
        if (dest[3][6].isForeground()) {
            dest[3][7] = dest[3][6];
            dest[4][6] = dest[3][6];
            dest[4][7] = dest[3][6];
        }
        // set color of R for C, U, A, T and O
        if (dest[7][5].isForeground()) {
            dest[6][5] = dest[7][5];
            dest[6][6] = dest[7][5];
            dest[6][7] = dest[7][5];
            dest[7][6] = dest[7][5];
            dest[7][7] = dest[7][5];
        }
    }

    // correct color of a lot words due crazy alignment
    if (G.clockTypeDef == Eng08x08 && (G.transitionColorize != CHARACTERS)) {
        // set color of TWENTY
        if (dest[2][1].isForeground()) {
            dest[0][1] = dest[0][0];
            dest[1][0] = dest[0][0];
            dest[1][1] = dest[0][0];
            dest[2][0] = dest[0][0];
            dest[2][1] = dest[0][0];
        }
        // set color of TEN (minute)
        else if (dest[0][0].isForeground()) {
            dest[1][0] = dest[0][0];
            dest[1][1] = dest[0][0];
        }
        // set color of FIVE (minute)
        if (dest[1][2].isForeground()) {
            dest[0][2] = dest[1][2];
            dest[0][3] = dest[1][2];
            dest[1][3] = dest[1][2];
        }
        // set color of FIFTEEN
        if (dest[0][4].isForeground()) {
            dest[0][2] = dest[0][4];
            dest[0][3] = dest[0][4];
            dest[0][5] = dest[0][4];
            dest[1][3] = dest[0][4];
            dest[1][4] = dest[0][4];
            dest[1][5] = dest[0][4];
        }
        // set color of HALF
        if (dest[0][6].isForeground()) {
            dest[0][7] = dest[0][6];
            dest[1][6] = dest[0][6];
            dest[1][7] = dest[0][6];
        }
        // set color of TEN (hour)
        if (dest[2][7].isForeground()) {
            dest[3][7] = dest[2][7];
            dest[4][7] = dest[2][7];
        }
        // set color of ELEVEN
        if (dest[3][6].isForeground()) {
            dest[3][5] = dest[3][6];
            dest[3][7] = dest[3][6];
            dest[4][5] = dest[3][6];
            dest[4][6] = dest[3][6];
            dest[4][7] = dest[3][6];
        }
        // set color of FIVE (hour)
        if (dest[4][0].isForeground() && dest[5][1].isForeground()) {
            dest[5][1] = dest[4][0];
            dest[6][2] = dest[4][0];
            dest[7][3] = dest[4][0];
        }
        // set color of NINE
        if (dest[4][4].isForeground() && dest[5][4].isForeground()) {
            dest[5][4] = dest[4][4];
            dest[6][4] = dest[4][4];
            dest[7][4] = dest[4][4];
        }
    }
}

//------------------------------------------------------------------------------

void Transition::saveMatrix() {
    static bool firstRun = true;
    copyMatrix(old, act);
    analyzeColors(act, STRIPE, foreground, background);
    foregroundMinute = foreground;
    if (isColorization()) {
        colorize(act);
    }
    if (firstRun) {
        firstRun = false;
        copyMatrix(work, act);
    }
    return;
}

//------------------------------------------------------------------------------
// copy (internal matrix or from LED stripe) and determine foreground and
// background color

void Transition::analyzeColors(RgbfColor **dest, RgbfColor **source,
                               RgbfColor &foreground, RgbfColor &background) {
    RgbfColor color, color1(0), color2(0);
    uint32_t colorCounter1 = 0, colorCounter2 = 0;
    const uint8_t numLEDsPerLetter = getLedsPerLetter(G.buildTypeDef);
    for (uint8_t row = 0; row < maxRows; row++) {
        for (uint8_t col = 0; col < maxCols; col++) {
            if (source == STRIPE) {
                color = RgbfColor(
                    led.getPixel(usedClockType->getFrontMatrixIndex(row, col) *
                                 numLEDsPerLetter));
            } else {
                color = source[row][col];
            }
            if (dest != NULL) {
                dest[row][col] = color;
            }
            if (color == color1) {
                colorCounter1++;
            } else {
                if (color == color2) {
                    colorCounter2++;
                } else {
                    // no color assigned yet
                    if (colorCounter1 > 0) {
                        color2 = color;
                        colorCounter2 = 1;
                    } else {
                        color1 = color;
                        colorCounter1 = 1;
                    }
                }
            }
        }
    }
    if (colorCounter1 > colorCounter2) { // Majority vote ?!
        background = color1;
        foreground = color2;
    } else {
        background = color2;
        foreground = color1;
    }
    foreground.setForeground(true);
    foreground.setOverlay(false);
    background.setForeground(false);
    background.setOverlay(false);
    if (dest != NULL) {
        for (uint8_t row = 0; row < maxRows; row++) {
            for (uint8_t col = 0; col < maxCols; col++) {
                dest[row][col].setForeground(dest[row][col] == foreground);
            }
        }
    }
}

//------------------------------------------------------------------------------
// Overwrite the LEDs with internal matrix

void Transition::copy2Stripe(RgbfColor **source) {
    for (uint8_t row = 0; row < maxRows; row++) {
        for (uint8_t col = 0; col < maxCols; col++) {
            led.setPixel(
                row, col,
                HsbColor{RgbColor(source[row][col].R, source[row][col].G,
                                  source[row][col].B)});
        }
    }
}

//------------------------------------------------------------------------------

void Transition::copyMatrix(RgbfColor **dest, RgbfColor **source) {
    for (uint8_t row = 0; row < maxRows; row++) {
        memcpy(dest[row], source[row], sizeofColumn);
    }
}

//------------------------------------------------------------------------------

void Transition::copyMatrixFlags(RgbfColor **dest, RgbfColor **source) {
    for (uint8_t row = 0; row < maxRows; row++) {
        for (uint8_t col = 0; col < maxCols; col++) {
            dest[row][col].setFlags(source[row][col].getFlags());
        }
    }
}

//------------------------------------------------------------------------------

void Transition::fillMatrix(RgbfColor **matrix, RgbfColor color) {
    for (uint8_t row = 0; row < maxRows; row++) {
        for (uint8_t col = 0; col < maxCols; col++) {
            matrix[row][col] = color;
        }
    }
}

//------------------------------------------------------------------------------

bool Transition::changesInTransitionTypeDurationOrDemo() {
    return (transitionType != lastTransitionType) ||
           (G.transitionDuration != lastTransitionDuration) ||
           (G.transitionDemo != lastTransitionDemo);
}

//------------------------------------------------------------------------------

uint16_t Transition::reverse(uint16_t num, bool mirrored,
                             uint8_t grafic_cols = 11) {
    // reverse left bits
    if (mirrored) {
        uint16_t res = 0;
        for (uint8_t i = 0; i < grafic_cols; i++) {
            if (num & (1 << i)) {
                res |= (1 << (grafic_cols - 1)) >> i;
            }
        }
        num = res;
    }
    return num;
}

//------------------------------------------------------------------------------
// slow == 1 -> 5s
// mid  == 2 -> 3.5s
// fast == 3 -> 2s

uint16_t Transition::calcDelay(uint16_t frames) {
    uint32_t pause;
    if (frames == 0) { // avoid div 0
        frames = 10;
    }
    switch (G.transitionDuration) {
    case 1:
        pause = 2000 / frames;
        break; // 2 seconds
    case 3:
        pause = 5000 / frames;
        break; // 5 seconds
    default:
        pause = 3500 / frames;
        break; // 3.5 seconds
    }
    if (pause == 0) {
        pause = 1;
    }
    return pause;
}

//------------------------------------------------------------------------------

void Transition::setPixelForChar(uint8_t col, uint8_t row, uint8_t offsetCol,
                                 unsigned char unsigned_d1, HsbColor color,
                                 fontSize font = normalSizeASCII) {
    if (led.getCharCol(font, col, row, unsigned_d1)) {
        work[row + 1][col + offsetCol].changeRgb(color);
    }
}

//------------------------------------------------------------------------------
// Transitions
//------------------------------------------------------------------------------

//------------------------------------------------------------------------------
// the new matrix slides in from above       | below
//                      row                  |               row
// phase | 9876543210   old  act   wechsel   | 9876543210   old  act   wechsel
//       | unten oben                        | unten oben
//   1   | aaaaaaaaan   0-8  9     0         | naaaaaaaaa   1-9  0     9
//   2   | aaaaaaaann   0-7  8-9   1         | nnaaaaaaaa   2-9  0-1   8
//   3   | aaaaaaannn   0-6  7-9   2         | nnnaaaaaaa   3-9  0-2   7
//   4   | aaaaaannnn   0-5  6-9   3         | nnnnaaaaaa   4-9  0-3   6
//   5   | aaaaannnnn   0-4  5-9   4         | nnnnnaaaaa   5-9  0-4   5
//   6   | aaaannnnnn   0-3  4-9   5         | nnnnnnaaaa   6-9  0-5   4
//   7   | aaannnnnnn   0-4  3-9   6         | nnnnnnnaaa   7-9  0-6   3
//   8   | aannnnnnnn   0-1  2-9   7         | nnnnnnnnaa   8-9  0-7   2
//   9   | annnnnnnnn   0    1-9   8         | nnnnnnnnna   9    0-8   1
//  10   | nnnnnnnnnn        0-9   9         | nnnnnnnnnn        0-9   0

uint16_t Transition::transitionScrollDown(bool dirDown) {
    uint32_t wechsel, rowAlt, rowNeu;
    bool copyFromNeu;

    if (phase == 1) {
        transitionDelay = calcDelay(maxRows) / 4;
    }
    if (dirDown) {
        wechsel = phase;
        rowAlt = 0;
        rowNeu = maxRows - phase;
    } else {
        wechsel = maxRows - phase;
        rowAlt = phase;
        rowNeu = 0;
    }
    for (uint8_t row = 0; row < maxRows; row++) {
        copyFromNeu = (row >= wechsel) ^ dirDown;
        for (uint8_t col = 0; col < maxCols; col++) {
            if (copyFromNeu) {
                work[row][col] = act[rowNeu][col];
            } else {
                work[row][col] = old[rowAlt][col];
            }
        }
        if (copyFromNeu) {
            rowNeu++;
        } else {
            rowAlt++;
        }
    }
    if (phase >= maxRows) {
        return 0;
    }
    return phase + 1;
}

//------------------------------------------------------------------------------
// the new matrix slides in from the right / in from the left
//                       col
// phase | 01234567890   old  act   Wechsel  01234567890   old  act   Wechsel
//   1   | aaaaaaaaaan   1-10 0      0       naaaaaaaaaa   0-9  10    10
//   2   | aaaaaaaaann   2-10 0-1    1       nnaaaaaaaaa   0-8  9-10   9
//   3   | aaaaaaaannn   3-10 0-2    2       nnnaaaaaaaa   0-7  8-10   8
//
//  10   | annnnnnnnnn   10   0-9    9       nnnnnnnnnna   0    1-10   1
//  11   | nnnnnnnnnnn        0-10  10       nnnnnnnnnnn        0-10   0

uint16_t Transition::transitionScrollRight(bool dirRight) {
    uint32_t wechsel, colAlt, colNeu;
    bool copyFromNeu;

    if (phase == 1) {
        transitionDelay = calcDelay(maxCols) / 4;
    }
    if (dirRight) {
        wechsel = phase;
        colAlt = 0;
        colNeu = maxCols - phase;
    } else {
        wechsel = maxCols - phase;
        colAlt = phase;
        colNeu = 0;
    }
    for (uint8_t col = 0; col < maxCols; col++) {
        copyFromNeu = (col >= wechsel) ^ dirRight;
        for (uint8_t row = 0; row < maxRows; row++) {
            if (copyFromNeu) {
                work[row][col] = act[row][colNeu];
            } else {
                work[row][col] = old[row][colAlt];
            }
        }
        if (copyFromNeu) {
            colNeu++;
        } else {
            colAlt++;
        }
    }
    if (phase >= maxCols) {
        return 0;
    }
    return phase + 1;
}

//------------------------------------------------------------------------------
// In each column, one ball falls from the highest letter.

uint16_t Transition::transitionBalls() {
    static uint32_t starttime;
    static uint32_t numBalls;
    uint32_t oldR, row, col, ballsDown;
    uint32_t timeDelta, now;

    if (phase == 1) {
        transitionDelay = 50; // 20 Frames per second
        numBalls = 0;
        for (col = 0; (col < maxCols) && (numBalls < maxCols); col++) {
            for (row = 0; (row < maxRows) && (numBalls < maxRows); row++) {
                if (work[row][col].isForeground()) {
                    balls[numBalls].begin(row, col, work[row][col], background,
                                          100 * numBalls);
                    numBalls++;
                    break;
                }
            }
        }
        starttime = millis();
    }

    now = millis();
    timeDelta = now - starttime;
    starttime = now;
    ballsDown = 0;
    for (uint8_t i = 0; i < numBalls; i++) {
        oldR = balls[i].row;
        ballsDown += balls[i].move(timeDelta);
        row = balls[i].row; // row, col new coordinates
        col = balls[i].col;
        if (row > oldR) { // down
            for (; row > oldR; oldR++) {
                work[oldR][col] = background;
            }
        } else { // up
            for (; row < oldR; oldR--) {
                work[oldR][col] = background;
            }
        }
        work[row][col] = balls[i].color;
    }
    if (ballsDown >= numBalls) {
        copyMatrix(work, act);
        return 0;
    }
    return phase + 1;
}

//------------------------------------------------------------------------------

uint16_t Transition::transitionFire() {
    static const uint8_t blendingFrames = 20;
    static bool sparkle, mirrored = false;
    static uint32_t subPhase;

    if (phase == 1) {
        // FIRE_1 .. 6 + 4 = 10
        transitionDelay = calcDelay(blendingFrames * 10) / 2;
        sparkle = false;
        subPhase = 1;
        firework->prepare(0, _white, FIRE_1, mirrored);
        if (transitionType == BIRTHDAY &&
            usedClockType->hasSpecialWordHappyBirthday()) {
            /*
            On birthdays, a fireworks animation appears every 5 minutes.
            Compatible clock types will display the words “Happy Birthday”
            instead of the time during the animation. Birthdays before 1900 are
            not animated.
            */
            fillMatrix(work, background);
            HsbColor hsbColor = HsbColor(foreground);
            hsbColor.H = pseudoRandomHue();

            led.clear();
            usedClockType->show(FrontWord::happy_birthday);
            led.setbyFrontMatrix(hsbColor);
            analyzeColors(work, STRIPE, foreground, background);

            copyMatrix(act, work);
        } else {
            // use current colors to be blended to act
            copyMatrix(old, work);
            copyMatrixFlags(work, act);
        }
        phase++;
    }

    bool lastSubPhase = subPhase == blendingFrames;
    if (subPhase > blendingFrames) {
        subPhase = 1;
        switch (phase) {
        case FIRE_4:
            firework->prepare(0, _red, FIRE_4, mirrored);
            break;
        case FIRE_5:
            firework->prepare(0, _red, FIRE_5, mirrored);
            break;
        case FIRE_6:
            firework->prepare(0, _red, FIRE_6, mirrored);
            break;
        case (FIRE_6 + 1):
            firework->prepare(0, _blue, FIRE_6, mirrored);
            firework->prepare(1, _green, FIRE_4, mirrored);
            firework->prepare(2, _yellow, FIRE_5, mirrored);
            break;
        case (FIRE_6 + 2):
            transitionDelay *= 2;
            sparkle = true;
            break;
        case (FIRE_6 + 3):
            break;
        case (FIRE_6 + 4):
            mirrored = !mirrored;
            copyMatrix(old, act); // old contains artefacts
            if ((transitionType == NEWYEAR_FIRE) ||
                (transitionType == BIRTHDAY)) {
                // While NEWYEAR_FIRE or BIRTHDAY repeat transition any 500ms
                // (will be stopped by changing transitionType)
                transitionDelay = 500;
                return 1; // restart transition
            }
            return 0; // end transition
            break;
        default:
            firework->prepare(0, _white, static_cast<BitmapSymbol>(phase),
                              mirrored);
        }
        phase++;
    }

    RgbColor overlayColor;
    float progress = static_cast<float>(subPhase) / blendingFrames;
    if (progress > 1.0) {
        progress = 1.0;
    }
    float fading =
        static_cast<float>((phase - FIRE_1) * blendingFrames + subPhase) /
        (blendingFrames * (FIRE_6 - FIRE_1 + 2));
    if (fading > 1.0) {
        fading = 1.0;
    }
    bool overlay;

    for (uint8_t col = 0; col < maxCols; col++) {
        for (uint8_t row = 0; row < maxRows; row++) {
            overlay = firework->getPixel(row, col, overlayColor);
            if (sparkle) {
                if (work[row][col].isOverlay()) {
                    // overlayed in previous run
                    work[row][col] = old[row][col]; // restore color
                    work[row][col].setOverlay(false);
                } else {
                    if (overlay && (random(10) == 0) && (!lastSubPhase)) {
                        old[row][col] = work[row][col]; // save color
                        work[row][col].changeRgb(_white);
                        work[row][col].setOverlay();
                    }
                }
            } else {
                // blend old -> act
                RgbColor color =
                    color.LinearBlend(old[row][col], act[row][col], fading);
                if (overlay && !lastSubPhase) {
                    // blend in overlay
                    overlayColor =
                        overlayColor.LinearBlend(color, overlayColor, progress);
                    work[row][col].changeRgb(overlayColor);
                    work[row][col].setOverlay();
                } else {
                    if (work[row][col].isOverlay()) {
                        // blend out overlay
                        color =
                            color.LinearBlend(overlayColor, color, progress);
                        work[row][col].changeRgb(color);
                        if (lastSubPhase) {
                            work[row][col].setOverlay(false);
                        }
                    } else {
                        // set mix of old and act
                        work[row][col].changeRgb(color);
                    }
                }
            }
        }
    }
    subPhase++;
    return phase;
}

//------------------------------------------------------------------------------

uint16_t Transition::transitionCountdown(struct tm &tm) {
    static int8_t lastSecond = 0, countDown = 59;
    uint8_t _second = tm.tm_sec; // 0 - 59
    if (_second != lastSecond) {
        if (phase == 1) { // Initialize at start of animation
            transitionDelay = 50;
            lastSecond = 0;
            countDown = 59;
        }
        if (countDown < 0) { // Countdown finished?
            lastSecond = 0;
            countDown = 59;
            return 0;
        }
        lastSecond = _second;
        fillMatrix(work, background);
        HsbColor hsbColor_1 = HsbColor(foreground);
        HsbColor hsbColor_2 = HsbColor(foreground);
        hsbColor_1.H = pseudoRandomHue();
        hsbColor_2.H = pseudoRandomHue();
        char seconds[8];
        // start 23:59:00     60 - 0
        snprintf(seconds, sizeof(seconds), "%d", countDown);
        // determine font size according layout
        // fontSize usedFontSize = determineFontSize(); // not applicable due to
        // linkage to digital clock
        fontSize usedFontSize = normalSizeASCII;
        // convert second to acii
        unsigned char unsigned_s0 = static_cast<unsigned char>(seconds[0]);
        unsigned char unsigned_s1 = static_cast<unsigned char>(seconds[1]);
        if (maxCols < (pgm_read_byte(&(fontWidth[usedFontSize])) * 2 + 1) ||
            maxRows < pgm_read_byte(&(fontHeight[usedFontSize]))) {
            usedFontSize = smallSizeNumbers;
            // convert char to int due to differt definition in Font.h
            unsigned_s0 -= 48;
            unsigned_s1 -= 48;
        }
        // for (uint8_t i = 0; i < 5; i++) {
        for (uint8_t row = 0; row < 8; row++) {     // row
            for (uint8_t col = 0; col < 5; col++) { // column
                if (countDown >= 10) {
                    // 1. Number without Offset
                    setPixelForChar(col, row, 0, unsigned_s0, hsbColor_1,
                                    usedFontSize);
                    // 2. Number with Offset
                    setPixelForChar(col, row, 6, unsigned_s1, hsbColor_2,
                                    usedFontSize);
                } else {
                    setPixelForChar(col, row, 3, unsigned_s0, hsbColor_1,
                                    usedFontSize);
                }
            }
        }
        countDown--;
        phase++;
    }
    return phase;
}

//------------------------------------------------------------------------------

void Transition::transitionColorChange() {
    static uint32_t lastTimeColor = 0;
    static uint32_t pauseZeitColor = 50;

    if (isColorization() && (G.transitionSpeed > 0)) {
        uint32_t now = millis();
        if (now >= (lastTimeColor + pauseZeitColor)) {
            lastTimeColor = now;
            float deltaHue = fmod(1.0 / (G.transitionSpeed * 20.0), 1.0);
            HsbColor hsbColor;
            for (uint8_t row = 0; row < maxRows; row++) {
                for (uint8_t col = 0; col < maxCols; col++) {
                    if (work[row][col].isForeground()) {
                        hsbColor = HsbColor(work[row][col]);
                        hsbColor.H = fmod(hsbColor.H + deltaHue, 1.0);
                        work[row][col].changeRgb(hsbColor);
                    }
                }
            }
            hsbColor = HsbColor(foregroundMinute);
            hsbColor.H = fmod(hsbColor.H + deltaHue, 1.0);
            foregroundMinute = RgbColor(hsbColor);
        }
    }
}

//------------------------------------------------------------------------------

uint16_t Transition::transitionLaser() {
    static uint8_t row = 0, col = 0;
    static bool loeschPhase = true;
    static RgbfColor strahl(255);

    if (phase == 1) {
        transitionDelay = calcDelay(maxRows * maxCols * 2);
        row = 0;
        col = 0;
        copyMatrix(work, old);
        loeschPhase = true;
    }

    if (loeschPhase) {
        work[row][col] = background;
    } else {
        work[row][col] = act[row][col];
    }

    if (++col >= maxCols) {
        col = 0;
        row++;
    }
    if (row < maxRows) {
        work[row][col] = strahl;
    } else {
        row = 0;
        if (loeschPhase == false) {
            return 0;
        }
        loeschPhase = false;
    }
    return phase + 1;
}

//------------------------------------------------------------------------------

uint16_t Transition::transitionFade() {
    uint16_t frames = 100;
    RgbColor color;

    if (phase == 1) {
        transitionDelay = calcDelay(frames);
        // copyMatrix(old, work);
    }
    float progress = static_cast<float>(phase) / static_cast<float>(frames);

    for (uint8_t col = 0; col < maxCols; col++) {
        for (uint8_t row = 0; row < maxRows; row++) {
            color = color.LinearBlend(old[row][col], act[row][col], progress);
            work[row][col].changeRgb(color);
        }
    }
    if (phase >= frames) {
        copyMatrix(work, act); // take all color.Foreground's from act
        return 0;
    }
    return phase + 1;
}

//------------------------------------------------------------------------------

uint16_t Transition::transitionMatrixRain() {
    uint16_t frames = 100;
    int8_t row, col;
    RgbfColor fadeColor;
    RgbaColor rainColor;

    if (phase == 1) {
        transitionDelay = calcDelay(frames);
        copyMatrix(old, work); // work is still the previous transition array
        uint8_t stop;
        uint8_t brightness = foreground.CalculateBrightness();
        for (col = 0; col < maxCols; col++) {
            stop = maxRows - 1;
            for (row = maxRows - 1; row >= 0; row--) {
                if (work[row][col].isForeground()) {
                    stop = row;
                    break;
                }
            }
            rain[col].begin(frames, stop, brightness);
        }
    }
    float progress = static_cast<float>(phase) / static_cast<float>(frames);
    for (col = 0; col < maxCols; col++) {
        for (row = 0; row < maxRows; row++) {
            fadeColor =
                fadeColor.LinearBlend(old[row][col], act[row][col], progress);
            rainColor = rain[col].get(row);
            rainColor = rainColor.LinearBlend(fadeColor, rainColor,
                                              rainColor.getAlpha());
            work[row][col].changeRgb(rainColor);
        }
    }
    if (phase >= frames) {
        copyMatrix(work, act); // take all color.Foreground's from act
        return 0;
    }
    return phase + 1;
}

//------------------------------------------------------------------------------

uint16_t Transition::transitionSnake() {
    uint16_t food = 40;

    if (phase == 1) {
        transitionDelay = calcDelay(food);
        snake->begin(this);
    }

    if (!snake->drawSnake()) {
        return 0;
    }
    return phase + 1;
}

//------------------------------------------------------------------------------
// Loop Helper Functions
//------------------------------------------------------------------------------

void Transition::demoMode(uint8_t &_hour, uint8_t &_minute, uint8_t _second) {
    static uint8_t test_second = _second;
    static uint8_t test_minute = _minute;
    static uint8_t test_hour = _hour;
    if (G.transitionDemo) {
        // increment every second
        // by checking isIdle transitions are completely done
        if (isIdle() && ((_second % 2) == 0) && (test_second != _second)) {
            // select increment by clock type
            if (usedClockType != nullptr) {
                if (usedClockType->hasOnlyQuarterLayout()) {
                    test_minute += 15;
                } else if (usedClockType->has60MinuteLayout()) {
                    test_minute += 1;
                } else {
                    test_minute += 5;
                }
            }
            // add one hour every 60 minutes
            if (test_minute >= 60) {
                test_minute %= 60;
                test_hour = (test_hour + 1) % 24;
            }
            // log demo time
            Serial.printf("Demo time: %02d:%02d\n", test_hour, test_minute);
        }
        // set to time variables
        _hour = test_hour;
        _minute = test_minute;
        test_second = _second;
    }
}

//------------------------------------------------------------------------------

void Transition::initTransitionStart() {
    nextActionTime = 0;
    phase = 1;
}

//------------------------------------------------------------------------------
// TODO: This function is used in two different functions:
// 1) Transition::isOverwrittenByTransition
// 2) Transition::loop
// It looks like that it is intended that function 1 and 2 both can reset the
// "MinuteChanged" status, so that only the first function calling the
// Transition::hasMinuteChanged is executed!?
// Are there better implementations which are more obvious?

bool Transition::hasMinuteChanged() {
    if (lastMinute != _minute) {
        lastMinute = _minute;
        return true;
    }
    return false;
}

//------------------------------------------------------------------------------
// 'WordclockChanges::Parameters', e.g. color modifications -> Apply w/o Trans
// 'WordclockChanges::Minute', e.g. minute iterations -> Apply w/o Transition
// 'WordclockChanges::Words', e.g. word changes -> Apply with Transition

bool Transition::isOverwrittenByTransition(WordclockChanges changesInWordMatrix,
                                           uint8_t minute) {
    if (transitionType == NO_TRANSITION) {
        if (changesInWordMatrix != WordclockChanges::Parameters &&
            hasMinuteChanged()) {
            // Needed in Case the Transition is switched off
            matrixChanged = true;
        }
    } else {
        if (changesInWordMatrix != WordclockChanges::Parameters) {
            if (changesInWordMatrix == WordclockChanges::Words ||
                changesInWordMatrix == WordclockChanges::Layout) {
                initTransitionStart();
            }
            lastMinute = minute;
            if (changesInWordMatrix != WordclockChanges::Minute) {
                matrixChanged = true;
            }
            return false;
        } else {
            if (changeBrightness()) {
                copy2Stripe(work);
            }
            return isIdle();
        }
    }
    return true;
}

//------------------------------------------------------------------------------

void Transition::init() { saveMatrix(); }

//------------------------------------------------------------------------------
// Loop Functions
//------------------------------------------------------------------------------

void Transition::loop(struct tm &tm) {
    static bool specialEvent;

    if (maxRows != usedClockType->rowsWordMatrix() ||
        maxCols != usedClockType->colsWordMatrix()) {

        static bool alreadyReported = false;
        if (!alreadyReported) {
            alreadyReported = true;
            Serial.println(F("[ERROR] Transition: buffer geometry mismatch"));
        }
        return;
    }

    if (G.prog == COMMAND_IDLE || G.prog == COMMAND_MODE_WORD_CLOCK) {
        specialEvent = isSpecialEvent(transitionType, tm, hasMinuteChanged());

        if (!specialEvent) {
            transitionType =
                getTransitionType(matrixChanged); // hasMinuteChanged()
        }

        if (matrixChanged) {
            matrixChanged = false;
            if (isColorization() && (G.transitionSpeed > 0)) {
                copyMatrix(act, work);
            }
            saveMatrix();
            copyMatrix(work, act);
        }

        if (transitionType == NO_TRANSITION) {
            if (changesInTransitionTypeDurationOrDemo()) {
                lastTransitionType = transitionType;
                copyMatrix(work, act);
                colorize(work);
                copy2Stripe(work);
                led.show();
            }
        } else {
            if (changesInTransitionTypeDurationOrDemo()) {
                lastTransitionType = transitionType;
                lastTransitionDemo = G.transitionDemo;
                lastTransitionDuration = G.transitionDuration;
                phase = 1;
            }
            if (G.transitionColorize != lastTransitionColorize) {
                lastTransitionColorize = G.transitionColorize;
                colorize(isIdle() ? work : act);
            }

            uint32_t now = millis();
            if ((!isIdle()) && (now >= nextActionTime)) {
                nextActionTime = now + transitionDelay;
                // Serial.printf("Transition: type %d phase %d\n",
                // transitionType,phase);
                switch (transitionType) {
                case ROLL_UP:
                    phase = transitionScrollDown(false);
                    break;
                case ROLL_DOWN:
                    phase = transitionScrollDown(true);
                    break;
                case SHIFT_LEFT:
                    phase = transitionScrollRight(false);
                    break;
                case SHIFT_RIGHT:
                    phase = transitionScrollRight(true);
                    break;
                case FADE:
                    phase = transitionFade();
                    break;
                case LASER:
                    phase = transitionLaser();
                    break;
                case MATRIX_RAIN:
                    phase = transitionMatrixRain();
                    break;
                case BALLS:
                    phase = transitionBalls();
                    break;
                case BIRTHDAY:
                case NEWYEAR_FIRE:
                case FIRE:
                    phase = transitionFire();
                    break;
                case SNAKE:
                    phase = transitionSnake();
                    break;
                case COLORED:
                    copyMatrix(work, act);
                    phase = 0;
                    break;
                case NEWYEAR_COUNTDOWN:
                    phase = transitionCountdown(tm);
                    break;
                case RANDOM:
                case NO_TRANSITION:
                    break;
                }
            }
            transitionColorChange();
            copy2Stripe(work);
            if (!specialEvent) {

                if (G.minuteVariant != MinuteVariant::Off) {
                    led.setbyMinuteArray(Foreground);
                }

                if (G.secondVariant != SecondVariant::Off) {
                    led.setbySecondArray(Frame);
                    // Workaround: setbySecondArray not in 'work'
                }
            }
            led.show();
        }
    }
}
