ESPWortuhr/Multilayout-ESP-Wordclock/include/Symbols.h

#pragma once

#define SYMBOL_11X10_ROWS 10
#define SYMBOL_11X10_COLS 11

const uint16_t symbol_11x10[][11] PROGMEM = {
    {0b00011111000,  // 0  WLAN100  0: . . . 0 0 0 0 0 . . . : 10
     0b01111111110,  // 1          21: . 0 0 0 0 0 0 0 0 0 . : 11
     0b11100000111,  // 2          22: 0 0 0 . . . . . 0 0 0 : 32
     0b10011111001,  // 3          43: 0 . . 0 0 0 0 0 . . 0 : 33
     0b00111111100,  // 4          44: . . 0 0 0 0 0 0 0 . . : 54
     0b00100000100,  // 5          65: . . 0 . . . . . 0 . . : 55
     0b00000100000,  // 6          66: . . . . . 0 . . . . . : 76
     0b00001110000,  // 7          87: . . . . 0 0 0 . . . . : 77
     0b00000100000,  // 8          88: . . . . . 0 . . . . . : 98
     0b00000000000}, // 9         109: . . . . . . . . . . . : 99

    {0b00000000000,  // 0  FIRE1    0: . . . . . . . . . . . : 10
     0b00000000000,  // 1          21: . . . . . . . . . . . : 11
     0b00000000000,  // 2          22: . . . . . . . . . . . : 32
     0b00000000000,  // 3          43: . . . . . . . . . . . : 33
     0b00000000000,  // 4          44: . . . . . . . . . . . : 54
     0b00000000000,  // 5          65: . . . . . . . . . . . : 55
     0b00000000000,  // 6          66: . . . . . . . . . . . : 76
     0b00000000000,  // 7          87: . . . . . . . . . . . : 77
     0b00000000000,  // 8          88: . . . . . . . . . . . : 98
     0b00100000000}, // 9         109: . . 0 . . . . . . . . : 99

    {0b00000000000,  // 0  FIRE2    0: . . . . . . . . . . . : 10
     0b00000000000,  // 1          21: . . . . . . . . . . . : 11
     0b00000000000,  // 2          22: . . . . . . . . . . . : 32
     0b00000000000,  // 3          43: . . . . . . . . . . . : 33
     0b00000000000,  // 4          44: . . . . . . . . . . . : 54
     0b00000000000,  // 5          65: . . . . . . . . . . . : 55
     0b00000000000,  // 6          66: . . . . . . . . . . . : 76
     0b00010000000,  // 7          87: . . . 0 . . . . . . . : 77
     0b00100000000,  // 8          88: . . 0 . . . . . . . . : 98
     0b00000000000}, // 9         109: . . . . . . . . . . . : 99

    {0b00000000000,  // 0  FIRE3    0: . . . . . . . . . . . : 10
     0b00000000000,  // 1          21: . . . . . . . . . . . : 11
     0b00000000000,  // 2          22: . . . . . . . . . . . : 32
     0b00000000000,  // 3          43: . . . . . . . . . . . : 33
     0b00000100000,  // 4          44: . . . . . 0 . . . . . : 54
     0b00001000000,  // 5          65: . . . . 0 . . . . . . : 55
     0b00001000000,  // 6          66: . . . . 0 . . . . . . : 76
     0b00000000000,  // 7          87: . . . . . . . . . . . : 77
     0b00000000000,  // 8          88: . . . . . . . . . . . : 98
     0b00000000000}, // 9         109: . . . . . . . . . . . : 99

    {0b00000000000,  // 0  FIRE4    0: . . . . . . . . . . . : 10
     0b00000000000,  // 1          21: . . . . . . . . . . . : 11
     0b00000010000,  // 2          22: . . . . . . 0 . . . . : 32
     0b00000101000,  // 3          43: . . . . . 0 . 0 . . . : 33
     0b00000010000,  // 4          44: . . . . . . 0 . . . . : 54
     0b00000000000,  // 5          65: . . . . . . . . . . . : 55
     0b00000000000,  // 6          66: . . . . . . . . . . . : 76
     0b00000000000,  // 7          87: . . . . . . . . . . . : 77
     0b00000000000,  // 8          88: . . . . . . . . . . . : 98
     0b00000000000}, // 9         109: . . . . . . . . . . . : 99

    {0b00000000000,  // 0  FIRE5    0: . . . . . . . . . . . : 10
     0b00000010000,  // 1          21: . . . . . . 0 . . . . : 11
     0b00000101000,  // 2          22: . . . . . 0 . 0 . . . : 32
     0b00001000100,  // 3          43: . . . . 0 . . . 0 . . : 33
     0b00000101000,  // 4          44: . . . . . 0 . 0 . . . : 54
     0b00000010000,  // 5          65: . . . . . . 0 . . . . : 55
     0b00000000000,  // 6          66: . . . . . . . . . . . : 76
     0b00000000000,  // 7          87: . . . . . . . . . . . : 77
     0b00000000000,  // 8          88: . . . . . . . . . . . : 98
     0b00000000000}, // 9         109: . . . . . . . . . . . : 99

    {0b00000111000,  // 0  FIRE6    0: . . . . . 0 0 0 . . . : 10
     0b00001000100,  // 1          21: . . . . 0 . . . 0 . . : 11
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
     0b10011001,  // 3          31: 0 . . 0 0 . . 0 : 24
     0b10011001,  // 4          32: 0 . . 0 0 . . 0 : 39
     0b10100101,  // 5          47: 0 . 0 . . 0 . 0 : 40
     0b01000010,  // 6          48: . 0 . . . . 0 . : 49
     0b00111100}, // 7          57: . . 0 0 0 0 . . : 50

    {0b00110000,  // 0  STBY     0: . . 0 0 . . . . :  7
     0b00011000,  // 1          15: . . . 0 0 . . . :  8
     0b00111100,  // 2          16: . . 0 0 0 0 . . : 23
     0b01011010,  // 3          31: . 0 . 0 0 . 0 . : 24
     0b11000011,  // 4          32: 0 0 . . . . 0 0 : 39
     0b11000011,  // 5          47: 0 0 . . . . 0 0 : 40
     0b01000010,  // 6          48: . 0 . . . . 0 . : 49
     0b00111100}, // 7          57: . . 0 0 0 0 . . : 50
};
