ESPWortuhr/Multilayout-ESP-Wordclock/Wortuhr/WebPage_Adapter.h

#pragma once

#include "WebSocketsServer.h"
#include "WebPageWortuhr.h"
#include "Uhr.h"
#include "Network.h"

#define RESPONSE_SIZE    900

class WebPage_Adapter : public WebSocketsServer {

public:
    // forward the port to the parent class constructor
    WebPage_Adapter(int port) : WebSocketsServer(port) {
    }

    /**
     * @param client WSclient_t *  ptr to the client struct
     */
    void handleNonWebsocketConnection(WSclient_t *client) override {
        DEBUG_WEBSOCKETS("[WS-Server][%d][handleHeader] no Websocket connection close.\n", client->num);
        client->tcp->write("HTTP/1.1 200 OK\r\n"
                           "Server: arduino-WebSocket-Server\r\n"
                           "Content-Type: text/html\r\n"
                           //--                    "Content-Length: 32\r\n"
                           "Connection: close\r\n"
                           //--                    "Sec-WebSocket-Version: 13\r\n"
                           "\r\n");
		Send_HTML_Code(client, 0);
        if (G.Colortype == Grbw){ Send_HTML_Code(client, 1);};
		Send_HTML_Code(client, 2);
        if (G.UhrtypeDef == Uhr_242){ Send_HTML_Code(client, 3);};
        if (G.UhrtypeDef == Uhr_169){ Send_HTML_Code(client, 4);};
        Send_HTML_Code(client, 5);
		if (G.UhrtypeDef == Uhr_114_Alternative){ Send_HTML_Code(client, 6);};
		Send_HTML_Code(client, 7);
        clientDisconnect(client);
    }

    void Send_HTML_Code(const WSclient_t *client, uint8_t index) const {
        char str[RESPONSE_SIZE + 4];
        unsigned ww = 0;
        unsigned yy = 0;
        int j;
        while (ww < HTML_Size[index]) {
            str[yy] = pgm_read_byte(&html_code[index][ww]);
            str[yy + 1] = '\0';
            yy++;
            if (yy == RESPONSE_SIZE) {
                j = strlen(str);
                client->tcp->write(&str[0], j);
                str[0] = '\0';
                yy = 0;
            }
            ww++;
        }
        if (yy > 0) {
            j = strlen(str);
            client->tcp->write(&str[0], j);
        }
    }

};

//-- WebSocketserver
WebPage_Adapter webSocket = WebPage_Adapter(80);

//------------------------------------------------------------------------------

uint16_t split(uint8_t *payload, uint8_t start, uint8_t lenght) {
    char buffer[lenght];
	uint8_t m = 0;
    for (uint16_t k = start; k < (start + lenght); k++) {
        buffer[m] = payload[k];
        m++;
    }
    return atoi(buffer);
}

//------------------------------------------------------------------------------

void payloadTextHandling(const uint8_t *payload, char* text, uint8_t length){
	uint8_t ii = 0;
	for (uint8_t k = 9; k < 9 + length; k++)
	{
		text[ii] = payload[k];
		ii++;
	}
	uint8_t index = 0;
	for (int8_t counter = length - 1; counter > -1; counter--)
	{
		if (!isSpace(text[counter]))
		{
			index = counter;
			break;
		}
	}
	text[index + 1] = '\0';
}

//------------------------------------------------------------------------------

void webSocketEvent(uint8_t num, WStype_t type, uint8_t *payload, size_t lenght) {
	//Disable Accesspoint Mode Disable Timer on Web Event
	if (AP_Status > 0){
		AP_Status = 0;
	}
    int ii;
    int jj;
    char tmp[30];
    payload = (payload == NULL) ? (uint8_t *) "" : payload;
    Serial.printf("Client-Nr.: [%u]  WStype: %u payload: %s\n", num, type, payload);

    switch (type) {
        case WStype_DISCONNECTED: {
            Serial.printf("[%u] Disconnected!\n", num);
            break;
        }
        case WStype_CONNECTED: {
            IPAddress ip = webSocket.remoteIP(num);
            Serial.printf("[%u] Connected from %d.%d.%d.%d url: %s\n", num, ip[0], ip[1], ip[2], ip[3], payload);
            break;
        }
        case WStype_TEXT:
		{
			Serial.printf("[%u] get Text: %s\n", lenght, payload);

			uint16_t command = split (payload, 0, 3);
			G.param1 = split (payload, 3, 3);
			G.param2 = split (payload, 6, 3);

			switch (command)
			{
				case COMMAND_MODE_WORD_CLOCK:
				{        // Uhrzeit Vordergrund Farbe einstellen
					G.prog = COMMAND_MODE_WORD_CLOCK;
					G.rgb[Foreground][0] = split (payload, 9, 3);
					G.rgb[Foreground][1] = split (payload, 12, 3);
					G.rgb[Foreground][2] = split (payload, 15, 3);
					G.rgb[Foreground][3] = split (payload, 18, 3);

					G.rgb[Background][0] = split (payload, 21, 3);
					G.rgb[Background][1] = split (payload, 24, 3);
					G.rgb[Background][2] = split (payload, 27, 3);
					G.rgb[Background][3] = split (payload, 30, 3);

					G.rgb[Frame][0] = split (payload, 33, 3);
					G.rgb[Frame][1] = split (payload, 36, 3);
					G.rgb[Frame][2] = split (payload, 39, 3);
					G.rgb[Frame][3] = split (payload, 42, 3);

					G.rgb[Effect][0] = split (payload, 45, 3);
					G.rgb[Effect][1] = split (payload, 48, 3);
					G.rgb[Effect][2] = split (payload, 51, 3);
					G.rgb[Effect][3] = split (payload, 54, 3);
					break;
				}

					//------------------------------------------------------------------------------

				case COMMAND_MODE_SECONDS:
				{      // Sekunden
					G.prog = COMMAND_MODE_SECONDS;
					if (G.param1 == 0) { G.prog_init = 1; }

					G.rgb[Effect][0] = split (payload, 45, 3);
					G.rgb[Effect][1] = split (payload, 48, 3);
					G.rgb[Effect][2] = split (payload, 51, 3);
					G.rgb[Effect][3] = split (payload, 54, 3);
					G.hell = split (payload, 57, 3);
					G.geschw = split (payload, 60, 3);
					break;
				}

					//------------------------------------------------------------------------------

				case COMMAND_MODE_MARQUEE:
				{      // Laufschrift
					G.prog = COMMAND_MODE_MARQUEE;
					if (G.param1 == 0) { G.prog_init = 1; }

					G.rgb[Effect][0] = split (payload, 45, 3);
					G.rgb[Effect][1] = split (payload, 48, 3);
					G.rgb[Effect][2] = split (payload, 51, 3);
					G.rgb[Effect][3] = split (payload, 54, 3);
					G.hell = split (payload, 57, 3);
					G.geschw = split (payload, 60, 3);
					break;
				}

					//------------------------------------------------------------------------------

				case COMMAND_MODE_RAINBOW:
				{      // Regenbogen
					G.prog = COMMAND_MODE_RAINBOW;
					G.prog_init = 1;

					G.hell = split (payload, 57, 3);
					G.geschw = split (payload, 60, 3);
					break;
				}

					//------------------------------------------------------------------------------

				case COMMAND_MODE_CHANGE:
				{      // Farbwechsel
					G.prog = COMMAND_MODE_CHANGE;
					G.prog_init = 1;

					G.hell = split (payload, 57, 3);
					G.geschw = split (payload, 60, 3);
					break;
				}

					//------------------------------------------------------------------------------

				case COMMAND_MODE_COLOR:
				{      // Farbe
					G.prog = COMMAND_MODE_COLOR;
					G.prog_init = 1;

					G.rgb[Effect][0] = split (payload, 45, 3);
					G.rgb[Effect][1] = split (payload, 48, 3);
					G.rgb[Effect][2] = split (payload, 51, 3);
					G.rgb[Effect][3] = split (payload, 54, 3);
					break;
				}

					//------------------------------------------------------------------------------

				case COMMAND_BRIGHTNESS:
				{      // Helligkeit
					G.hell = split (payload, 57, 3);
					break;
				}

					//------------------------------------------------------------------------------

				case COMMAND_SPEED:
				{       // Geschwindigkeit
					G.geschw = split (payload, 60, 3);
					break;
				}

					//------------------------------------------------------------------------------

				case COMMAND_SET_INITIAL_VALUES:
				{       // Startwerte speichern
					G.conf = COMMAND_SET_INITIAL_VALUES;
					break;
				}

					//------------------------------------------------------------------------------

				case COMMAND_SET_TIME:
				{       // Uhrzeit setzen
					G.conf = COMMAND_SET_TIME;
					ii = 0;
					tmp[0] = '\0';
					uint32_t  tt = split(payload, 12, 16);
					Serial.println(tt);
					for (uint8_t k = 12; k < 28; k++)
					{
						tmp[ii] = payload[k];
						ii++;
					}
					tt = atoi(tmp);
					Serial.println(tt);
					Serial.printf("Conf: Time: %d\n", tt);
					setTime(tt);
					break;
				}

					//------------------------------------------------------------------------------

				case COMMAND_SET_HOSTNAME:
				{         // Hostname speichern
					G.conf = COMMAND_SET_HOSTNAME;
					uint32_t  tt = split(payload, 12, 16);
					ii = 0;
					for (uint8_t k = 9; k < 25; k++)
					{
						if (payload[k] != ' ')
						{
							G.hostname[ii] = payload[k];
							ii++;
						}
					}
					G.hostname[ii] = '\0';
					break;
				}

					//------------------------------------------------------------------------------

				case COMMAND_SET_SETTING_SECOND:
				{       // Anzeige Sekunden speichern
					G.conf = COMMAND_SET_SETTING_SECOND;
					G.zeige_sek = split (payload, 9, 3);
					break;
				}

					//------------------------------------------------------------------------------

				case COMMAND_SET_MINUTE:
				{       // Anzeige Minuten speichern
					G.conf = COMMAND_SET_MINUTE;
					G.zeige_min = split (payload, 9, 3);
					break;
				}

					//------------------------------------------------------------------------------

				case COMMAND_SET_LDR:
				{       // LDR speichern
					G.conf = COMMAND_SET_LDR;
					G.ldr = split (payload, 9, 3);
					G.ldrCal = split (payload, 12, 3);
					break;
				}

					//------------------------------------------------------------------------------

				case COMMAND_SET_LANGUAGE_VARIANT:
				{       // LDR speichern
					G.conf = COMMAND_SET_LANGUAGE_VARIANT;
					G.Sprachvariation[ItIs15] = split(payload,9, 3);
					G.Sprachvariation[ItIs20] = split(payload,12, 3);
					G.Sprachvariation[ItIs40] = split(payload,15, 3);
					G.Sprachvariation[ItIs45] = split(payload,18, 3);
					break;
				}

					//------------------------------------------------------------------------------

				case COMMAND_SET_MQTT:
				{       // MQTT Daten speichern
					G.conf = COMMAND_SET_MQTT;
					G.MQTT_State = split (payload, 9, 3);
					G.MQTT_Port = split (payload, 12, 5);
                    ii = 0;
					for (uint8_t k = 17; k < 47; k++)
					{
						if (payload[k] != ' ')
						{
							G.MQTT_Server[ii] = payload[k];
							ii++;
						}
					}
					G.MQTT_Server[ii] = '\0';
					break;
				}

					//------------------------------------------------------------------------------

				case COMMAND_SET_TIME_MANUAL:
				{       // Uhrzeit manuell setzen
					G.conf = COMMAND_SET_TIME_MANUAL;
					int temp_std= split (payload, 9, 3);
					int temp_min = split (payload, 12, 3);
					setTime(temp_std, temp_min, 0, 1, 12, 2020);
					break;
				}

					//------------------------------------------------------------------------------

				case COMMAND_SET_WPS_MODE:
				{       // Aktivieren des WPS Modus
					G.conf = COMMAND_SET_WPS_MODE;
					break;
				}

					//------------------------------------------------------------------------------

				case COMMAND_SET_COLORTYPE:
				{       // ColorType speichern
					G.conf = COMMAND_SET_COLORTYPE;
					G.Colortype = split (payload, 9, 3);
					break;
				}

					//------------------------------------------------------------------------------

				case COMMAND_SET_UHRTYPE:
				{       // UhrType speichern
					G.conf = COMMAND_SET_UHRTYPE;
					G.UhrtypeDef = split (payload, 9, 3);
					break;
				}

					//------------------------------------------------------------------------------

				case COMMAND_SET_WEATHER_DATA:
				{       // Openweathermap speichern
					G.conf = COMMAND_SET_WEATHER_DATA;
					ii = 0;
					for (uint8_t k = 9; k < 16; k++)
					{
						if (payload[k] != ' ')
						{
							G.cityid[ii] = payload[k];
							ii++;
						}
					}
					G.cityid[ii] = '\0';
					//
					jj = 0;
					for (uint8_t l = 17; l < 49; l++)
					{
						if (payload[l] != ' ')
						{
							G.apikey[jj] = payload[l];
							jj++;
						}
					}
					G.apikey[jj] = '\0';
					break;
				}

					//------------------------------------------------------------------------------

				case COMMAND_SET_BRIGHTNESS:
				{       // Helligkeit speichern
					G.conf = COMMAND_SET_BRIGHTNESS;
					G.h6 = split (payload, 9, 3);
					G.h8 = split (payload, 12, 3);
					G.h12 = split (payload, 15, 3);
					G.h16 = split (payload, 18, 3);
					G.h18 = split (payload, 21, 3);
					G.h20 = split (payload, 24, 3);
					G.h22 = split (payload, 27, 3);
					G.h24 = split (payload, 30, 3);
					break;
				}

					//------------------------------------------------------------------------------

				case COMMAND_SET_MARQUEE_TEXT:
				{       // Lauftext speichern
					G.conf = COMMAND_SET_MARQUEE_TEXT;
					payloadTextHandling(payload, G.ltext, sizeof(G.ltext) / sizeof(G.ltext[0]));
					break;
				}

					//------------------------------------------------------------------------------

				case COMMAND_SET_TIMESERVER:
				{       // Zeitserver speichern
					G.conf = COMMAND_SET_TIMESERVER;
                    payloadTextHandling(payload, G.zeitserver, sizeof(G.zeitserver) / sizeof(G.zeitserver[0]));
					break;
				}

					//------------------------------------------------------------------------------

				case COMMAND_SET_BOOT:
				{       // Bootoptionen speichern
					G.conf = COMMAND_SET_BOOT;
					G.bootLedBlink = split (payload, 9, 3);
					G.bootLedSweep = split (payload, 12, 3);
					G.bootShowWifi = split (payload, 15, 3);
					G.bootShowIP = split (payload, 18, 3);
					break;
				}
					//------------------------------------------------------------------------------

				case COMMAND_SET_WIFI_DISABLED:
				{       // Zeitserver speichern
					G.conf = COMMAND_SET_WIFI_DISABLED;
					break;
				}

					//------------------------------------------------------------------------------

				case COMMAND_SET_WIFI_AND_RESTART:
				{       // WLAN-Daten löschen und neu starten
					G.conf = COMMAND_SET_WIFI_AND_RESTART;
					break;
				}

					//------------------------------------------------------------------------------

				case COMMAND_RESET:
				{      // Reset
					G.conf = COMMAND_RESET;
					break;
				}

					//------------------------------------------------------------------------------

				case COMMAND_REQUEST_CONFIG_VALUES:
				{      // Config anfordern
					G.conf = COMMAND_REQUEST_CONFIG_VALUES;
					G.client_nr = num;
					break;
				}

					//------------------------------------------------------------------------------

				case COMMAND_REQUEST_COLOR_VALUES:
				{      // Farbwerte anfordern
					G.conf = COMMAND_REQUEST_COLOR_VALUES;
					G.client_nr = num;
					break;
				}

					//------------------------------------------------------------------------------

				case COMMAND_REQUEST_WIFI_LIST:
				{      // Wlan Liste anfordern
					G.conf = COMMAND_REQUEST_WIFI_LIST;
					G.client_nr = num;
					break;
				}

					//------------------------------------------------------------------------------

				default:
					break;
			}
		}
        case WStype_BIN: {
            Serial.printf("[%u] get binary lenght: %u\n", num, lenght);
            hexdump(payload, lenght);
            //--echo data back to browser
            //webSocket.sendBIN(num, payload, lenght);
            break;
        }
        default:
            break;
    }
}
