ESPWortuhr/Multilayout-ESP-Wordclock/include/ClockWork.h

#pragma once

#include "HardwareButtonController.h"
#include <NeoPixelBus.h>

class ClockWork {
private:
    uint16_t countMillisSpeed = 0;
    uint32_t previousMillis = 0;
    uint32_t lux = 0;
    HardwareButtonController hardwareButtonController;

private:
    //------------------------------------------------------------------------------
    // Helper Functions
    //------------------------------------------------------------------------------
    void loopAutoBrightLogic();
    void loopHardwareButtons();
    void handleHardwareButtonAction(HardwareButtonAction action);
    void toggleHardwareButtonPower();
    void nextHardwareButtonMode();
    void nextHardwareButtonTransition();
    void increaseHardwareButtonBrightness();
    void nextHardwareButtonHue();
    void requestHardwareButtonDisplayRefresh();
    uint32_t num32BitWithOnesAccordingToColumns();

    //------------------------------------------------------------------------------
    // Front Effect Functions
    //------------------------------------------------------------------------------
    struct StaticScrollingText {
        uint8_t start = 0;
        uint8_t len = 0;
        uint8_t width = 0;
        uint8_t height = 0;
        uint8_t totalWidth = 0;
        bool onlyDigits = true;
    };

    void rainbow();
    void rainbowCycle();
    void rainbowSpiralCycle();
    bool getStaticScrollingTextInfo(const char *buf, StaticScrollingText &info);
    void displayStaticScrollingText(const char *buf,
                                    const StaticScrollingText &info);
    void scrollingText(const char *buf);
    void displaySymbols(BitmapSymbol bitmapSymbolnum);
    void countdownToMidnight();

    //------------------------------------------------------------------------------
    // Minute Functions
    //------------------------------------------------------------------------------
    void showSpecialWordBeen(const uint8_t min);
    void showMinuteInWords(uint8_t min);
    bool checkIfClockHasMinuteInWordsAndItIsSet();
    void showMinute(uint8_t min);
    void checkForValidLanguageVariant();
    void resetMinVariantIfNotAvailable();
    FrontWord getFrontWordForNum(uint8_t min);
    bool checkTwentyUsage();
    bool hasTwentyAndCheckForUsage();
    bool hasDreiviertelAndCheckForUsage();
    void setMinute(uint8_t min, uint8_t &offsetHour, bool &fullHour);

    //------------------------------------------------------------------------------
    // Hour Functions
    //------------------------------------------------------------------------------
    void setHour(uint8_t std, const bool fullHour);

    //------------------------------------------------------------------------------
    // Loop Helper Functions
    //------------------------------------------------------------------------------

    bool isMidnight(const uint8_t hour);
    WordclockChanges changesInClockface();
    void calcClockface();
    void setClock();
    void setDaytimeWords(uint8_t hour);
    void setItIs(uint8_t min, const uint8_t offsetHour);
    bool DetermineIfItIsIsShown(const uint8_t min);
    void DetermineWhichItIsToShow(uint8_t offsetHour, uint8_t min);
    void clearClockByProgInit();

public:
    // ClockWork() = default;
    ~ClockWork() = default;

    //------------------------------------------------------------------------------
    // Helper Functions
    //------------------------------------------------------------------------------
    ClockType *getPointer(uint8_t type);
    void initLedStrip(uint8_t num);
    void initHardwareButtons();
    uint32_t getLuxValue() const { return lux; }
    float getAdcValue() const {
        uint16_t adcRaw = analogRead(A0);
        float voltage = (adcRaw * 3.3f) / 1023.0f;
        return round(voltage * 100.0f) / 100.0f;
    }
    uint16_t getAdcRawValue() const { return analogRead(A0); }

    //------------------------------------------------------------------------------
    // Minute Functions
    //------------------------------------------------------------------------------
    uint8_t determineWhichMinuteVariant();

    //------------------------------------------------------------------------------
    // Boot Functions
    //------------------------------------------------------------------------------
    void initBootLed();
    void initBootLedBlink();
    void initBootLedSweep(uint32_t delay);
    void initBootShowIp(const char *buf);

    //------------------------------------------------------------------------------
    // Loop Functions
    //------------------------------------------------------------------------------
    void loop(struct tm &tm);
};
